hyperlode/luciebox/documentation/Drawings_F306/Luciebox_lid_layout_annotated_colour_font_autobahn.png

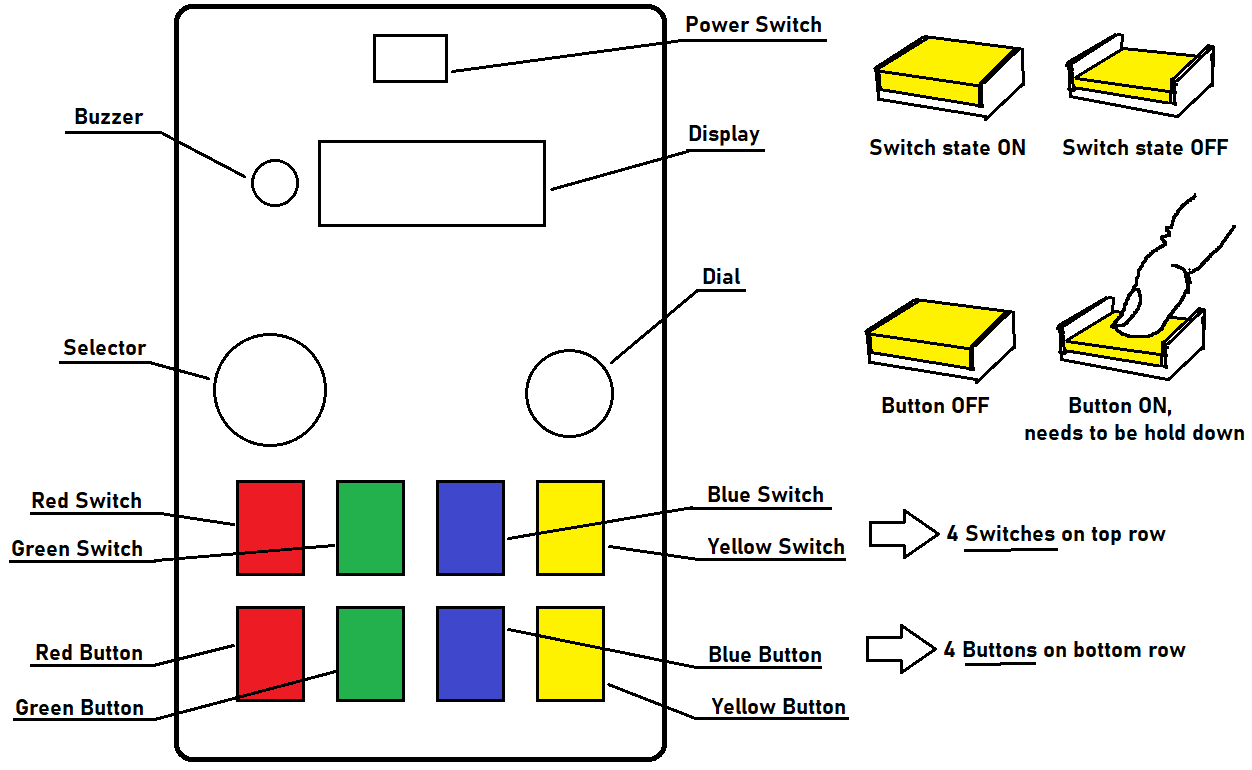
documentation/Drawings_F306/Luciebox_lid_layout_annotated_colour_font_autobahn.png
