hyperlode/luciebox/documentation/Drawings_F308/Luciebox_lid_layout_annotated_font_bahnschrift.png

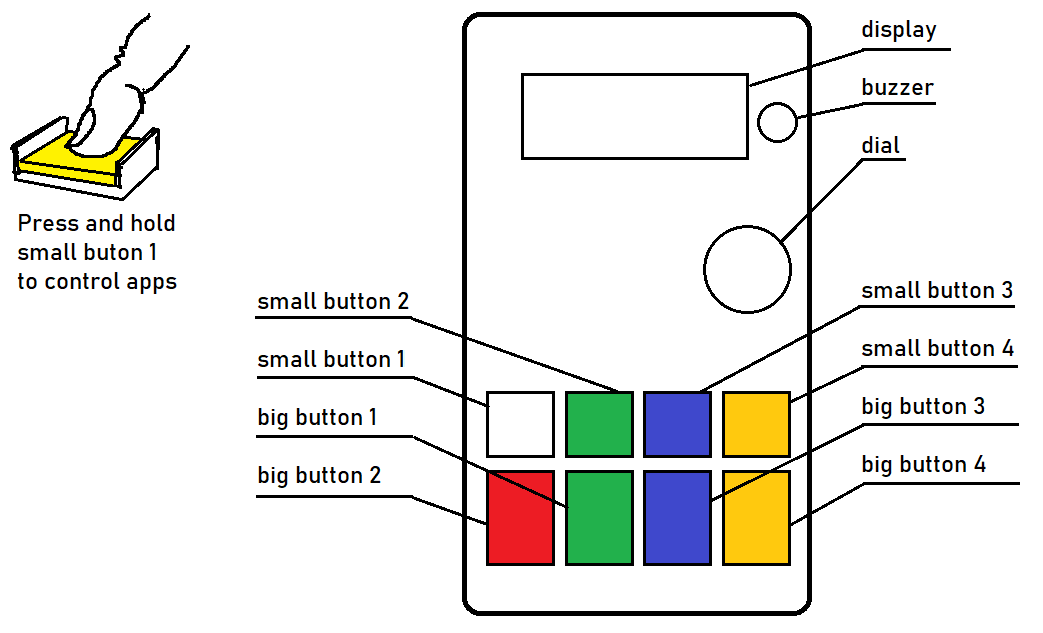
documentation/Drawings_F308/Luciebox_lid_layout_annotated_font_bahnschrift.png
