hyperlode/luciebox/pcb/v1 pcb with clouds - change pin 2 to A3 for segment B.jpg

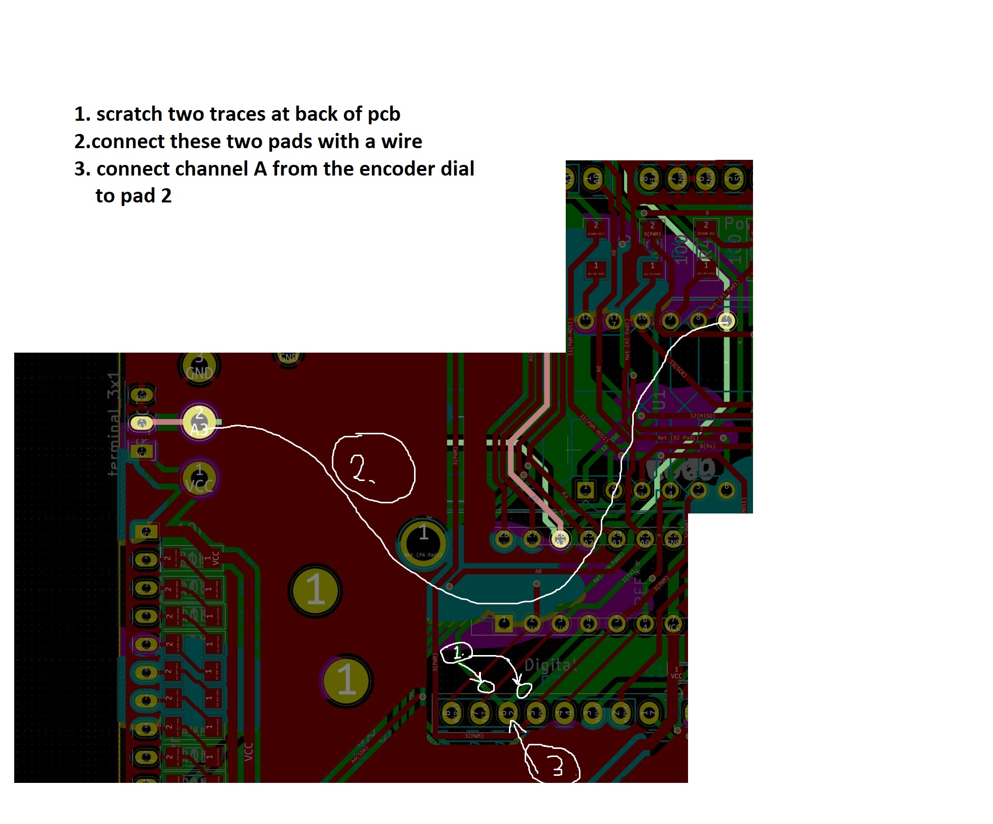
pcb/v1 pcb with clouds - change pin 2 to A3 for segment B.jpg
