hyperlode/luciebox/Luciebox/Apps.cpp

#include "Apps.h"
#include "PretbakSettings.h"

// ------------------------------------------------------------------------------------------------------------------------------------------------------
//		INIT AND ADMINISTRATION
// ------------------------------------------------------------------------------------------------------------------------------------------------------

Apps::Apps(){};

#ifdef ENABLE_SELECT_APPS_WITH_SELECTOR
void Apps::setPeripherals(BinaryInput binaryInputs[], RotaryEncoderDial *encoder_dial, DisplayManagement *ledDisp, LedMultiplexer5x8 *allLights, Buzzer *buzzer, PotentioSelector *selectorDial)
{
    this->buzzer = buzzer;
    this->binaryInputs = binaryInputs;
    this->encoder_dial = encoder_dial;
    this->ledDisp = ledDisp;
    this->allLights = allLights;
    this->selectorDial = selectorDial;

    textHandle = ledDisp->getDisplayTextBufHandle();
    decimalDotsHandle = ledDisp->getDecimalPointsHandle();
    inactivity_timer.setInitCountDownTimeSecs(indexToTimeSeconds(INACTIVITY_TIME_INDEX));
    resetInactivityTimer();
    always_on_timer.start();
}
#else
void Apps::setPeripherals(BinaryInput binaryInputs[], RotaryEncoderDial *encoder_dial, DisplayManagement *ledDisp, LedMultiplexer5x8 *allLights, Buzzer *buzzer)
{
    this->buzzer = buzzer;
    this->binaryInputs = binaryInputs;
    this->encoder_dial = encoder_dial;
    this->ledDisp = ledDisp;
    this->allLights = allLights;

    textHandle = ledDisp->getDisplayTextBufHandle();
    decimalDotsHandle = ledDisp->getDecimalPointsHandle();
    inactivity_timer.setInitCountDownTimeSecs(indexToTimeSeconds(INACTIVITY_TIME_INDEX));
    resetInactivityTimer();
    always_on_timer.start();

    appState = appStateInit;
}

#endif

#ifdef ENABLE_SELECT_APPS_WITH_SELECTOR
void Apps::appStateLoop()
{
    updateEveryAppCycleBefore();
    bool selector_changed = selectorDial->getValueChangedEdge();
    int selector_dial_value = selectorDial->getSelectorValue() - 1; // -1 because 13 resistor values for 12 pos knob, gnd is never switchted.

    bool shift_changed = (binaryInputsEdgeUp | binaryInputsEdgeDown) & (1 << BUTTON_INDEXED_SMALL_0); // l atching button acts as a "shift button" to have two apps per selector location

    // uint8_t selected_app = selector_dial_value * 2 + ((binaryInputsToggleValue & (1 << BUTTON_INDEXED_SMALL_0)) > 0);

    bool init_app_init = (selector_changed && (MODE_SETTINGS_SELECTOR != 10)) || (shift_changed && (selector_dial_value != 0)); // settings mode have no dual app available. So, don't init if shift button is toggled.  //&& (selector_dial_value != 11) and multitimer app

    this->app_init_edge = false;

    if (init_app_init)
    {
#ifdef ENABLE_SERIAL
        Serial.println("app select:");
        Serial.println(selected_app);
#endif

        buzzerSilentClearBuffer(); // The moment we switch apps, the sound goes off immediatly.

        // set to init state before a new app starts
        splash_screen_playing = true;
    }

    if (splash_screen_playing)
    {
        // do init routine (showing splash screen), if finished,end of init. Then continue to init of the chosen application
        splash_screen_playing = this->init_app(init_app_init, selector_dial_value);
        if (!splash_screen_playing)
        {
            this->initializeAppDataToDefault();
            this->app_init_edge = true;
            selected_app = selector_dial_value * 2 + ((binaryInputsToggleValue & (1 << BUTTON_INDEXED_SMALL_0)) > 0);
        }
    }

    // not as else statement, to have the init properly transferred after app beginning screen.
    if (!splash_screen_playing)
    {
        appSelector();
    }

    inactivityHandler();

    updateEveryAppCycleAfter();
}

#else

void Apps::appStateLoop()
{
    updateEveryAppCycleBefore();

#ifdef ENABLE_SELECT_APPS_WITH_SELECTOR
    bool selector_changed = selectorDial->getValueChangedEdge();
    int selector_dial_value = selectorDial->getSelectorValue() - 1; // -1 because 13 resistor values for 12 pos knob, gnd is never switchted.

#endif
    switch (appState)
    {

    case appStateInit:
    {
        this->selected_app = 1; // start with one, which also works for the non selector button setting

#ifdef ENABLE_EEPROM
#ifndef ENABLE_SELECT_APPS_WITH_SELECTOR
        // memorize active app
        this->selected_app = eeprom_read_byte(
            (uint8_t *)EEPROM_LUCIEBOX_ACTIVE_APP_AT_SHUTDOWN);
#endif
#endif
        appState = appSplashInit;
        selected_app_memory = 66;
        break;
    }

    case appSplashInit:
    {
#ifdef ENABLE_SERIAL
        Serial.println("app select:");
        Serial.println(selected_app);
#endif

        buzzerSilentClearBuffer(); // The moment we switch apps, the sound goes off immediatly.

        this->init_app(true, selected_app - 1); // selected app -1 because we start from 1
        // set to init state before a new app starts
        appState = appSplash;

        break;
    }

    case appSelection:
    {

        // reset app
        if ((binaryInputsEdgeUp & (1 << BUTTON_INDEXED_BIG_1)))
        {
            appState = appInit;
        }

        modifyValueUpDownWithButtonsBig2And3(&selected_app);
        selected_app += encoder_dial->getDelta();
        checkBoundaries(&selected_app, 1, 22, true);

        if (selected_app_edge != selected_app)
        {
            // set_blink_offset();
            blink_offset = millis();
        }
        selected_app_edge = selected_app;

        this->displayAllSegments = 0;

        if (switch_off)
        {
            setStandardTextToTextHANDLE(TEXT_OFF);
        }
        else
        {
            flashPictureToDisplayAllSegments(app_splash_screens + (selected_app - 1) * 4);
        }

        // activate switch off. shut down, will trigger when app selector is at negative edge
        if ((binaryInputsValue & (1 << BUTTON_INDEXED_BIG_0)))
        {
            switch_off = true;
        }

        if (!(binaryInputsValue & (1 << BUTTON_INDEXED_SMALL_0)))
        {
            // switch off. shut down
            if (switch_off)
            {
                shutdown();
            }

            if (selected_app == selected_app_memory)
            {
                // this->displayAllSegments = this->displayAllSegmentsBuffer;
                // displayAllSegmentsToScreen();
                appState = appRunning;
            }
            else
            {
                appState = appSplashInit;
            }
            selected_app_memory = selected_app;
        }

        // if (millis_quarter_second_period())
        // {
        //     lights |= 1 << LIGHT_BUTTON_BIG_0 | 1 << LIGHT_BUTTON_BIG_2 | 1 << LIGHT_BUTTON_BIG_3;
        // }
        button_light_blink_quarter_second_period(LIGHT_BUTTON_BIG_0);
        button_light_blink_quarter_second_period(LIGHT_BUTTON_BIG_2);
        button_light_blink_quarter_second_period(LIGHT_BUTTON_BIG_3);

        // if (millis_blink_250_750ms()){
        if ((millis() - blink_offset) > APP_NUMBER_TO_PICTOGRAM_DELAY_MILLIS)
        {
            ledDisp->setBinaryToDisplay(this->displayAllSegmentsBuffer);
            displayAllSegmentsToScreen();
        }
        else
        {
            ledDisp->setNumberToDisplayAsDecimal(selected_app);
        }

#ifndef ENABLE_SELECT_APPS_WITH_SELECTOR
        // small button lights off at app selection, whatever their toggle state is (but we do not want to lose the toggle state)
        for (uint8_t i = 5; i < 8; i++)
        {
            lights &= ~(1 << lights_indexed[i]);
        }
#endif

        break;
    }

    case appSplash:
    {

#ifdef ENABLE_SELECT_APPS_WITH_SELECTOR
        // do init routine (showing splash screen), if finished,end of init. Then continue to init of the chosen application
        splash_screen_playing = this->init_app(false, selector_dial_value);
        if (!splash_screen_playing)
        {
            // this->app_init_edge = true;
            appState = appInit;
            selected_app = selector_dial_value * 2 + ((binaryInputsToggleValue & (1 << BUTTON_INDEXED_SMALL_0)) > 0);
        }
#else
        // do init routine (showing splash screen), if finished,end of init. Then continue to init of the chosen application
        splash_screen_playing = this->init_app(false, selected_app - 1); // selected app -1 because we start from 1
        if (!splash_screen_playing)
        {
            appState = appInit;
        }

        if (binaryInputsValue & (1 << BUTTON_INDEXED_SMALL_0))
        {
            switch_off = false;
            appState = appSelection;
        }
#endif

        break;
    }

    case appInit:
    {
        this->initializeAppDataToDefault();
        this->app_init_edge = true;
        appState = appRunning;
        break;
    }

    case appRunning:
    {
        // not as else statement, to have the init properly transferred after app beginning screen.
        appSelector();
        this->app_init_edge = false; // global variable (saves memory) true at first run (set in another state )

#ifdef ENABLE_SELECT_APPS_WITH_SELECTOR

        bool shift_changed = (binaryInputsEdgeUp | binaryInputsEdgeDown) & (1 << BUTTON_INDEXED_SMALL_0); // l atching button acts as a "shift button" to have two apps per selector location

        // uint8_t selected_app = selector_dial_value * 2 + ((binaryInputsToggleValue & (1 << BUTTON_INDEXED_SMALL_0)) > 0);

        bool init_app_init = (selector_changed && (MODE_SETTINGS_SELECTOR != 10)) || (shift_changed && (selector_dial_value != 0)); // settings mode have no dual app available. So, don't init if shift button is toggled OR if we're visualizing the selector switch analog value in the settings app

        if (init_app_init)
        {
            appState = appSplashInit;
        }

#else
        if (binaryInputsValue & (1 << BUTTON_INDEXED_SMALL_0))
        {
            switch_off = false;
            appState = appSelection;
            // this->displayAllSegmentsBuffer = this->displayAllSegments; // if there is no change of app, the display state needs to be preserved
        }

#endif

        break;
    }
    }
    inactivityHandler();
    updateEveryAppCycleAfter();
}

#endif

void Apps::inactivityHandler()
{

    // for some timing aps, we want this watchdog timer to be disabled.
    // It's easily accomplished by resetting the inactivity timer in those apps continuously.

    // for every button press, the watchdog timer is reset
    if (binaryInputsEdgeUp)
    {
        resetInactivityTimer();
    }

    // watchdog timer elapsed
    if (inactivity_timer.getCountDownTimerElapsedAndRestart())
    {
        autoShutdown();
    }
}

void Apps::autoShutdown()
{
    // will shutdown if available and play an "I'm still on" sound if not.

#ifdef ENABLE_SOFT_POWER_OFF
    // auto power off

    uint8_t enable_auto_power_off = true;
#ifdef ENABLE_EEPROM
    enable_auto_power_off = !eeprom_read_byte((uint8_t *)EEPROM_LUCIEBOX_AUTO_POWER_OFF_DISABLED);
#endif
    if (enable_auto_power_off)
    {

        shutdown();
    }
    else
    {
        playSongHappyDryer();
    }

#else
    playSongHappyDryer();
#endif
}

void Apps::shutdown()
{
    // memorize active app to restart after shutdown
    eeprom_update_byte(
        (uint8_t *)EEPROM_LUCIEBOX_ACTIVE_APP_AT_SHUTDOWN,
        selected_app); // eeprom_update_... only writes if different from what's in address, no need to read to check.

    // add delay for eeprom to settle down? Fact is, without this delay, it does not save...
    for (uint16_t i = 0; i < 1000; i++)
    {
        resetInactivityTimer();
    }

    digitalWrite(PIN_POWER_ON_HOLD, LOW);
    digitalWrite(PIN_SELECTOR_BUTTON, LOW); // pull down input to enable transistor base to go low
    // normally, the device is switched off at this point. IF however, it's powered through an external device bypassing the auto power off mode, it should keep on working.

    for (uint16_t i = 0; i < 26000; i++)
    {
        resetInactivityTimer();
    }

    digitalWrite(PIN_POWER_ON_HOLD, HIGH);
    digitalWrite(PIN_SELECTOR_BUTTON, HIGH);
    // buzzerPlayDisappointment();
}

void Apps::appSelector()
{
    // #ifdef FUNCTION_POINTER_APP_SELECTION // problem: takes more memory than switch-case. AND init and initOnBigLatchInitToo not good. The solution would be to have all the apps without advanced init bundled together, and from certain selector value onwards and up, use "init"

    switch (selected_app)
    {
    case APP_SELECTOR_LETTERS_AND_CHARS:
#ifdef ENABLE_SCHOOL_APP
        this->modeCountingLettersAndChars();
#endif
        break;

    case APP_SELECTOR_SIMON:
#ifdef ENABLE_SIMON_APP
        this->modeSimon();
#endif
        break;

    case APP_SELECTOR_SOUND_NOTES:
        this->modeSoundNotes();
        break;

    case APP_SELECTOR_SOUND_COMPOSER:
        this->modeComposeSong();
        break;

    case APP_SELECTOR_STOPWATCH:
        stopwatch();
        break;

    case APP_SELECTOR_POMODORO:
#ifdef ENABLE_POMODORO
        pomodoroTimer();
#endif
        break;

    case APP_SELECTOR_RANDOMWORLD:
        this->modeRandomWorld();
        break;

    case APP_SELECTOR_TALLY_KEEPER:
#ifdef ENABLE_TALLY_KEEPER
        this->modeTallyKeeper();
#endif
        break;

    case APP_SELECTOR_GEIGER:
        this->modeGeiger();
        break;

    case APP_SELECTOR_HACK_TIME:
        this->modeHackTime();
        break;

    case APP_SELECTOR_SOUND_SONG:
        this->modeSoundSong();
        break;

    case APP_SELECTOR_DRAW:
        this->draw();
        break;

    case APP_SELECTOR_DRAW_GAME:
#ifdef ENABLE_DRAW_GAME
        this->drawGame();
#endif
        break;

    case APP_SELECTOR_MOVIE_MODE:
        this->modeMovie();
        break;

    case APP_SELECTOR_SETTING:
    case APP_SELECTOR_SETTING_TOO:
        this->modeSettings();
        break;

    case APP_SELECTOR_SOUND_METRONOME:
        this->modeMetronome();
        break;

    case APP_SELECTOR_SOUND_SEQUENCER:
        this->modeSequencer();
        break;

    case APP_SELECTOR_REACTION_GAME:
    case APP_SELECTOR_GUITAR_HERO:
#ifdef ENABLE_REACTION_APP
        this->modeReactionGame();
#endif
        break;

#ifdef ENABLE_TILT_APP
    case APP_SELECTOR_DREAMTIME:
        this->modeDreamtime();
        break;
    case APP_SELECTOR_TILT:
        this->tiltSwitchTest();
        break;
#else
    case APP_SELECTOR_DREAMTIME:
    case APP_SELECTOR_DREAMTIME_TOO:
        this->modeDreamtime();
        break;
#endif

#ifdef ENABLE_SHOOTOUT
    case APP_SELECTOR_SHOOTOUT:
        this->shootout();
        break;
#endif

    case APP_SELECTOR_MULTITIMER:
#ifdef ENABLE_MULTITIMER_STANDALONE_DEPRECATED
        this->miniMultiTimer();
#elif defined ENABLE_MULTITIMER_INTEGRATED
        this->multitimer_integrated();
#endif
        break;

    default:
        break;
    }
}

void Apps::resetInactivityTimer()
{
    inactivity_timer.start();
}

void Apps::updateEveryAppCycleBefore()
{
    binaryInputsEdgeUp = 0;
    binaryInputsEdgeDown = 0;
    binaryInputsValue = 0;
    binaryInputsToggleValue = 0;

    // it's important to realize the display is reset before every cycle. Do not forget to update it all the time.
    lights = 0x00;

    // load quick access bytes.
    for (uint8_t i = 0; i < 8; i++)
    {
        binaryInputsEdgeUp |= binaryInputs[buttons_indexed[i]].getEdgeUp() << i;
        binaryInputsEdgeDown |= binaryInputs[buttons_indexed[i]].getEdgeDown() << i;
        binaryInputsValue |= binaryInputs[buttons_indexed[i]].getValue() << i;
        binaryInputsToggleValue |= binaryInputs[buttons_indexed[i]].getToggleValue() << i;

#ifdef ENABLE_SELECT_APPS_WITH_SELECTOR
        lights |= binaryInputs[buttons_indexed[i]].getValue() << lights_indexed[i];

#else
        // by default: button lights on if activated
        if (i < 5)
        {
            // big buttons (i = 0,1,2,3) and control button (4) (small_0)
            // 5 instead of 4 because BUTTON_INDEXED_SMALL_0 is standard also only on if pressed.
            lights |= binaryInputs[buttons_indexed[i]].getValue() << lights_indexed[i];
        }
        else
        {
            // small buttons (i=5,6,7)
            lights |= binaryInputs[buttons_indexed[i]].getToggleValue() << lights_indexed[i];
        }
#endif
    }

    // big_buttons_mask =
    // byte big_buttons_mask = 1 << BUTTON_INDEXED_BIG_0 | 1 << BUTTON_INDEXED_BIG_1 | 1 << BUTTON_INDEXED_BIG_2 | 1 << BUTTON_INDEXED_BIG_3;

    binaryInputsEdgeUpBigButtonIndex = -1;
    // get index of pressed button.
    for (int i = 0; i < BIG_BUTTONS_COUNT; i++)
    {
        // WARNING: If button presses are pressed in too quick succession (and processed in the same cycle), only one edge is captured.
        // ONLY USE IN SLOW APPS
        if (binaryInputsEdgeUp & 1 << i)
        {
            // #ifdef ENABLE_SERIAL
            //             Serial.println(i);
            // #endif
            binaryInputsEdgeUpBigButtonIndex = i;
        }
    }

    setBlankDisplay();
}

void Apps::updateEveryAppCycleAfter()
{
    // setLedArray();
    ledDisp->setLedArray(lights);
}

void Apps::initializeAppDataToDefault()
{
    // allLights->setBrightness(0, false); // disable because it annoys me:)

    initiateCountDowntimerWith500Millis(&general_timer_1); //

    // buzzer  (buzzer off at init of splash screen)
    buzzer->setSpeedRatio(2);
    buzzer->setTranspose(0);

    // encoder
    encoder_dial->setRange(1023, true); // allow overflow. (this makes it different from the limited potentio.)
    encoder_dial->setValue(0);

    fill8BytesArrayWithZero();

    randomSeed(millis());

    encoder_dial->setSensitivity(8);

    // all shared variables to zero or false

    general_boolean1 = 0;
    general_boolean2 = 0;
    general_boolean3 = 0;
    general_boolean4 = 0;
    general_int16_t_1 = 0;
    general_int16_t_2 = 0;
    general_int16_t_3 = 0;
    general_int16_t_4 = 0;
    general_uint16_t_1 = 0;
    general_uint16_t_2 = 0;
    general_uint8_t_1 = 0;
    general_uint8_t_2 = 0;
    general_uint8_t_3 = 0;
    general_uint8_t_4 = 0;
    general_uint8_t_5 = 0;
    general_int8_t_1 = 0;
    general_long_1 = 0;
    general_long_2 = 0;

    // simulated l atching buttons reset. This is the great advantage of not having l atching buttons. The app starts in a truly blank state when initialized.
    for (uint8_t i = 0; i < 8; i++)
    {
        binaryInputs[buttons_indexed[i]].setToggleValue(0);
    }
}

bool Apps::init_app(bool init, uint8_t selector)
{
    // shows animated introduction splash screen at each main app startup
    // returns true as long as it is busy

    if (init)
    {
        // init of the init_app..
        this->displayAllSegments = 0;
        flashPictureToDisplayAllSegments(app_splash_screens + selector * 4);

        // initialize list
        randomSequence(FADE_IN_RANDOM_LIST, 32);

        // INIT_SPLASH_ANIMATION_STEP = 0;
        // INIT_SPLASH_LIGHTS_STEP = 0;

        this->TIMER_INIT_APP.start(-20);
    }

    // advance one frame
    if (this->TIMER_INIT_APP.getCountDownTimerElapsedAndRestart())
    {
        INIT_SPLASH_LIGHTS_STEP++;
        INIT_SPLASH_ANIMATION_STEP++;
    }

#ifdef ENABLE_SELECT_APPS_WITH_SELECTOR
    if (INIT_SPLASH_ANIMATION_STEP < 5)
    {
        lights = 0xff;
        // all lights on
        ledDisp->setBinaryToDisplay(0xFFFFFFFF); // use fade in as fade out to set text.
    }
    else
#endif
        if (INIT_SPLASH_ANIMATION_STEP < 23)
    {
        // show app splash screen
        ledDisp->setBinaryToDisplay(this->displayAllSegments);

        // ledDisp->setNumberToDisplayAsDecimal(MODE_SETTINGS_SELECTOR);
        // textBufToDisplay();

        lights = 0xff;
    }
    else if (INIT_SPLASH_ANIMATION_STEP < 55)
    {
        // fade out
        ledDisp->setBinaryToDisplay(~this->fadeInList(INIT_SPLASH_ANIMATION_STEP - 24, ~this->displayAllSegments, this->FADE_IN_RANDOM_LIST));
        INIT_APP_LIGHTS_COUNTER = ((32 - (INIT_SPLASH_ANIMATION_STEP - 22)) / 4);
        for (uint8_t i = 0; i <= INIT_APP_LIGHTS_COUNTER; i++)
        {
            lights |= 0x1 << lights_indexed_as_installed[i];
        }
    }
    else
    {
        return false;
    }

#ifdef ENABLE_SELECT_APPS_WITH_SELECTOR
    // hold down big button to freeze app splash screen (easier to rotate knob to search for desired app)
    byte big_buttons_mask = 1 << BUTTON_INDEXED_BIG_0 | 1 << BUTTON_INDEXED_BIG_1 | 1 << BUTTON_INDEXED_BIG_2 | 1 << BUTTON_INDEXED_BIG_3;
    if ((binaryInputsValue & big_buttons_mask) > 0)
    {
        INIT_SPLASH_ANIMATION_STEP = 6;
        lights = 0x00;
        lights |= 0x1 << lights_indexed_as_installed[(INIT_SPLASH_LIGHTS_STEP % 32) / 4];
        // lights	|= 0x1 << lights_indexed_as_installed[((INIT_SPLASH_LIGHTS_STEP+16) %32)/4];
    }
#endif

    return true;
}

// ------------------------------------------------------------------------------------------------------------------------------------------------------
//		ACTUAL APPS
// ------------------------------------------------------------------------------------------------------------------------------------------------------

void Apps::modeDreamtime()
{
    // baby activity for those who can not yet rotate the selector dial. (the shift button makes it stay in the same app).

    if (this->app_init_edge)
    {
        MODE_DREAMTIME_FADE_IN_ELSE_FADE_OUT = true;
        MODE_DREAMTIME_STEP = random(3, 31); // let's not start with an empty screen
    }

    modifyValueUpDownWithButtonsBig2And3(&MODE_DREAMTIME_STEP);

    if (!(binaryInputsToggleValue & (1 << BUTTON_INDEXED_SMALL_3)))
    {
        if (this->TIMER_DREAMTIME.getCountDownTimerElapsedAndRestart())
        {
            MODE_DREAMTIME_STEP++;
        }

        dialOnEdgeChangeInitTimerPercentage(&TIMER_DREAMTIME);
    }
    else
    {
        MODE_DREAMTIME_STEP += encoder_dial->getDelta();
    }

    if (!checkBoundaries(&MODE_DREAMTIME_STEP, 0, 31, true))
    {
        MODE_DREAMTIME_FADE_IN_ELSE_FADE_OUT = !MODE_DREAMTIME_FADE_IN_ELSE_FADE_OUT;
        randomSequence(MODE_DREAMTIME_RANDOM_LIST, 32);
    }

    if (binaryInputsEdgeUp & (1 << BUTTON_INDEXED_SMALL_1))
    {
        if (binaryInputsToggleValue & (1 << BUTTON_INDEXED_SMALL_1))
        {
            loadBuzzerTrack(SONG_ALPHABET);
        }
        else
        {
            playSongHappyDryer();
        }
    }

    if (!(binaryInputsToggleValue & (1 << BUTTON_INDEXED_SMALL_2)))
    {
        if (MODE_DREAMTIME_STEP_MEMORY != MODE_DREAMTIME_STEP)
        {
            // PROBLEM: random notes buffer and song buffer are the same bytes list! -->hence the weird behaviour
            buzzerSilentClearBufferAndAddNote(MODE_DREAMTIME_RANDOM_LIST[MODE_DREAMTIME_STEP]); // 60
            // if(buzzer->buzzerBufferDonePlaying()){
            //     addNoteToBuzzer(MODE_DREAMTIME_RANDOM_LIST[MODE_DREAMTIME_STEP]); //60

            // }
        }
    }

    uint32_t display_binary = fadeInList(MODE_DREAMTIME_STEP, 0, MODE_DREAMTIME_RANDOM_LIST);

    MODE_DREAMTIME_STEP_MEMORY = MODE_DREAMTIME_STEP;

    if (!MODE_DREAMTIME_FADE_IN_ELSE_FADE_OUT)
    {
        display_binary = ~display_binary;
    }

    if (binaryInputsValue & (1 << BUTTON_INDEXED_BIG_1))
    {
        display_binary = 0xFFFFFFFF;
        buzzerPlayApproval();
    }

    if (binaryInputsValue & (1 << BUTTON_INDEXED_BIG_0))
    {
        display_binary = 0x795E3F38; // self glorification time.
    }

    ledDisp->setBinaryToDisplay(display_binary);
}

#ifdef ENABLE_POMODORO

#ifndef ENABLE_SELECT_APPS_WITH_SELECTOR
void Apps::pomodoroTimer()
{
    uint8_t display_mode = POMODORO_DISPLAY_TIMER;

#ifdef POMODORO_ENABLE_HOURGLASS
    this->displayAllSegments = 0;
#endif

    lights = 0;

    if (encoder_dial->getDelta() != 0)
    {
        set_blink_offset();
    }

    if (this->app_init_edge)
    {
#ifdef ENABLE_EEPROM
        POMODORO_MAIN_CLOCK_TIME_INDEX = eeprom_read_byte((uint8_t *)EEPROM_POMODORO_INIT_TIME_INDEX);
        POMODORO_PAUSE_TIME_INDEX = eeprom_read_byte((uint8_t *)EEPROM_POMODORO_PAUSE_TIME_INDEX);
        POMODORO_PROBABILITY_BEEP_INTERVAL_INDEX = eeprom_read_byte((uint8_t *)EEPROM_POMODORO_RND_BEEP_TIME_INDEX);
#else
        POMODORO_MAIN_CLOCK_TIME_INDEX = POMODORO_INIT_DEFAULT_TIME_INDEX;
        POMODORO_PAUSE_TIME_INDEX = POMODORO_PAUSE_DEFAULT_TIME_INDEX;
        POMODORO_PROBABILITY_BEEP_INTERVAL_INDEX = POMODORO_PROBABILITY_BEEP_INTERVAL_DEFAULT_TIME_INDEX;
#endif
    }

    // acts as ticking mute on / off
    if (binaryInputsToggleValue & (1 << BUTTON_INDEXED_BIG_1))
    {
        lights |= 1 << LIGHT_BUTTON_BIG_1;
    }

    POMODORO_TIMER_TICKING = binaryInputsToggleValue & (1 << BUTTON_INDEXED_SMALL_3);
    // in main menu or timing? (run main menu at least once at init. Even when start button started) to initialize variables depending on settings buttons

    if (POMODORO_TIMER_TICKING && !app_init_edge)
    {
        // never auto power off when timer is on
        resetInactivityTimer();

        // pomodoro timer running

        if (!POMODORO_FIRST_TICKING_CYCLING_DONE)
        {
            POMODORO_FIRST_TICKING_CYCLING_DONE = true;
            POMODORO_IN_BREAK = false;
            // just started timing
            POMODORO_TIMER.start();
#ifdef ENABLE_EEPROM
            eeprom_update_byte((uint8_t *)EEPROM_POMODORO_INIT_TIME_INDEX, POMODORO_MAIN_CLOCK_TIME_INDEX);
            eeprom_update_byte((uint8_t *)EEPROM_POMODORO_PAUSE_TIME_INDEX, POMODORO_PAUSE_TIME_INDEX);
            eeprom_update_byte((uint8_t *)EEPROM_POMODORO_RND_BEEP_TIME_INDEX, POMODORO_PROBABILITY_BEEP_INTERVAL_INDEX);
#endif
        }

        if (binaryInputsEdgeUp & (1 << BUTTON_INDEXED_BIG_2))
        {
            POMODORO_STATS_WORKING_BAD++;
        }
        if (binaryInputsEdgeUp & (1 << BUTTON_INDEXED_BIG_3))
        {
            POMODORO_STATS_WORKING_GOOD++;
        }

        if ((binaryInputsValue & (1 << BUTTON_INDEXED_BIG_2)))
        {
            display_mode = POMODORO_DISPLAY_SHOW_BAD;
        }
        if ((binaryInputsValue & (1 << BUTTON_INDEXED_BIG_3)))
        {
            display_mode = POMODORO_DISPLAY_SHOW_GOOD;
        }

        // ticking sound / random checkup-beep
        // uint8_t tick_duration = encoder_dial->getValueLimited(160, false) / 2; // was 40, but set to 80 for less sensitivity. do again divide by four to limit options.
        // tick_duration += encoder
        stepChange(&POMODORO_SOUND, encoder_dial->getDelta(), 0, 80, false);
        bool tick_twice_a_second = POMODORO_SOUND > 40;
        // tick_duration = tick_duration % 40;

        if (POMODORO_TIMER.getEdgeSinceLastCallFirstGivenHundredsPartOfSecond(500, true, tick_twice_a_second))
        {
#ifdef POMODORO_ENABLE_HOURGLASS
            POMODORO_VISUAL_TIMER_PROGRESS =
                (uint8_t)((
                    (17 * POMODORO_TIMER.getTimeMillis()) / POMODORO_TIMER.getInitTimeMillis())

                );
#endif

            if (POMODORO_PROBABILITY_BEEP_INTERVAL_INDEX > 0)
            {
                if (random(0, indexToTimeSeconds(POMODORO_PROBABILITY_BEEP_INTERVAL_INDEX) * 2) <= 1 - (tick_twice_a_second))
                {
                    // random has 0 included. as we have to take into account the double ticking,
                    // calculate the probability in half a seconds. i.e.  one every minute: (0,120)
                    buzzerPlayDisappointment();
                };
            }

            // no sound when zero
            if (buzzer->buzzerBufferDonePlaying() &&                     // if end of clock signal sounds, no ticking! erase to optimize memory
                !(binaryInputsToggleValue & (1 << BUTTON_INDEXED_BIG_1)) // mute on / off
            )
            {
                // buzzer->playTone(500, 1 + (unsigned long)POMODORO_SOUND % 40); // works well
                buzzerPlayTone(500, 1 + (unsigned long)POMODORO_SOUND % 40);
            }
        }

        // timer
        if (getCountDownTimerHasElapsed(&POMODORO_TIMER))
        {
            POMODORO_IN_BREAK = !POMODORO_IN_BREAK;
            if (POMODORO_IN_BREAK)
            {
                // finished main pomodoro

                playSongHappyDryer();
                if (POMODORO_PAUSE_TIME_INDEX > 0)
                {
                    POMODORO_TIMER.setInitCountDownTimeSecs(indexToTimeSeconds(POMODORO_PAUSE_TIME_INDEX));
                    POMODORO_TIMER.start();
                }
                else
                {

#ifndef ENABLE_SELECT_APPS_WITH_SELECTOR
                    // with l atching buttons, we need to unlatch the button physically. But, with m omentary buttons, we can unlatch the button with software
                    binaryInputs[BUTTON_SMALL_3].setToggleValue(0);

#endif
                    POMODORO_TIMER.reset();
                    POMODORO_IN_BREAK = false;
                }
            }
            else
            {
                // coming out of break. Not executed at starting Pomodoro by switch.

                loadBuzzerTrack(SONG_ATTACK);
                POMODORO_TIMER.setInitCountDownTimeSecs(indexToTimeSeconds(POMODORO_MAIN_CLOCK_TIME_INDEX));
                POMODORO_TIMER.start();
            }
        }

        // inviting lights to press the buttons
        lights |= 1 << LIGHT_BUTTON_BIG_2;
        lights |= 1 << LIGHT_BUTTON_BIG_3;
#ifdef POMODORO_ENABLE_HOURGLASS
        if (binaryInputsToggleValue & (1 << BUTTON_INDEXED_BIG_0))
        {
            display_mode = POMODORO_DISPLAY_TIMER_HOURGLASS;
        }

#endif
    }
    else
    {
        // in main menu
        POMODORO_FIRST_TICKING_CYCLING_DONE = false;
        POMODORO_TIMER.reset();
        POMODORO_TIMER.setInitCountDownTimeSecs(indexToTimeSeconds(POMODORO_MAIN_CLOCK_TIME_INDEX));

        // set timer up for change
        int16_t *active_seconds_modifier = &POMODORO_MAIN_CLOCK_TIME_INDEX; // normal time setting is default option
        if ((binaryInputsValue & (1 << BUTTON_INDEXED_SMALL_2)))
        {

            active_seconds_modifier = &POMODORO_PAUSE_TIME_INDEX;
            display_mode = POMODORO_DISPLAY_PAUSE_INIT_SECS;
        }
        else if ((binaryInputsValue & (1 << BUTTON_INDEXED_SMALL_1)))
        {

            active_seconds_modifier = &POMODORO_PROBABILITY_BEEP_INTERVAL_INDEX;
            display_mode = POMODORO_DISPLAY_BEEP_PROBABILITY;
        }

        // look for value change with encoder dial
        encoderDialRefreshTimeIndex(active_seconds_modifier);

        // show performance results
        if ((binaryInputsValue & (1 << BUTTON_INDEXED_BIG_2)))
        {
            display_mode = POMODORO_DISPLAY_SHOW_BAD;
        }
        if ((binaryInputsValue & (1 << BUTTON_INDEXED_BIG_3)))
        {
            display_mode = POMODORO_DISPLAY_SHOW_GOOD;
        }

        // blinking small button invites user to start
        // if (millis_half_second_period())
        // {
        //     lights |= 1 << LIGHT_BUTTON_SMALL_3;
        // }
        button_light_blink_half_second_period(LIGHT_BUTTON_SMALL_3);
    }

    // display
    switch (display_mode)
    {
    case POMODORO_DISPLAY_TIMER_HOURGLASS:
    {
        setStandardTextToTextBuf(TEXT_SPACES);
#ifdef POMODORO_ENABLE_HOURGLASS
        // always set to buffer. later on it's decided if it's displayed or not.
        // for (uint8_t i=0;i<POMODORO_VISUAL_TIMER_PROGRESS;i++)
        // {
        // 	this->displayAllSegments |= 1UL << i;
        // }
        // this->displayAllSegments &= ~(1UL << 15); // keep seconds blinker spot clear
        // setBlankDisplay();
        lights |= 1 << LIGHT_BUTTON_BIG_0;
        flashPictureToDisplayAllSegments(disp_4digits_animations + FADE_IN_OFFSET + (POMODORO_VISUAL_TIMER_PROGRESS) * 4);
#endif
    }
    break;

    case POMODORO_DISPLAY_TIMER:
    {
        POMODORO_TIMER.getTimeString(textHandle);
        if (POMODORO_IN_BREAK)
        {
            setStandardTextToTextBuf(TEXT_PAUS);
        }
        else
        {
            POMODORO_TIMER.getTimeString(textBuf);
        }
    }
    break;

    case POMODORO_DISPLAY_PAUSE_INIT_SECS:
    {
        timeSecondsToClockString(textHandle, indexToTimeSeconds(POMODORO_PAUSE_TIME_INDEX));
        setStandardTextToTextBuf(TEXT_PAUS);
    }
    break;

    case POMODORO_DISPLAY_BEEP_PROBABILITY:
    {
        timeSecondsToClockString(textHandle, indexToTimeSeconds(POMODORO_PROBABILITY_BEEP_INTERVAL_INDEX));
        setStandardTextToTextBuf(TEXT_RANDOM_BEEP);
    }
    break;

    case POMODORO_DISPLAY_SHOW_GOOD:
    {
        setStandardTextToTextBuf(TEXT_YES);
        ledDisp->numberToBufAsDecimal(textHandle, POMODORO_STATS_WORKING_GOOD);
    }
    break;

    case POMODORO_DISPLAY_SHOW_BAD:
    {
        setStandardTextToTextBuf(TEXT_NO);
        ledDisp->numberToBufAsDecimal(textHandle, POMODORO_STATS_WORKING_BAD);
    }
    break;

    default:
        break;
    }

    displayTimerSecondsBlinker(&POMODORO_TIMER);

    // leds
    if (POMODORO_PROBABILITY_BEEP_INTERVAL_INDEX > 0)
    {
        lights |= 1 << LIGHT_BUTTON_SMALL_1;
    }
    if (POMODORO_PAUSE_TIME_INDEX > 0)
    {
        lights |= 1 << LIGHT_BUTTON_SMALL_2;
    }

#ifdef POMODORO_ENABLE_HOURGLASS
    displayAllSegmentsToScreen();
    if (millis_blink_250_750ms())
    {
        textBufToDisplay();
    }

#else
    if (millis_blink_250_750ms())
    {
        textBufToDisplay();
    }
#endif
}

#else // ENABLE_SELECT_APPS_WITH_SELECTOR
void Apps::pomodoroTimer()
{
    uint8_t display_mode = POMODORO_DISPLAY_TIMER;

#ifdef POMODORO_ENABLE_HOURGLASS
    this->displayAllSegments = 0;
#endif

    if (encoder_dial->getDelta() != 0)
    {
        set_blink_offset();
    }

    if (this->app_init_edge)
    {
#ifdef ENABLE_EEPROM
        POMODORO_MAIN_CLOCK_TIME_INDEX = eeprom_read_byte((uint8_t *)EEPROM_POMODORO_INIT_TIME_INDEX);
        POMODORO_PAUSE_TIME_INDEX = eeprom_read_byte((uint8_t *)EEPROM_POMODORO_PAUSE_TIME_INDEX);
        POMODORO_PROBABILITY_BEEP_INTERVAL_INDEX = eeprom_read_byte((uint8_t *)EEPROM_POMODORO_RND_BEEP_TIME_INDEX);
#else
        POMODORO_MAIN_CLOCK_TIME_INDEX = POMODORO_INIT_DEFAULT_TIME_INDEX;
        POMODORO_PAUSE_TIME_INDEX = POMODORO_PAUSE_DEFAULT_TIME_INDEX;
        POMODORO_PROBABILITY_BEEP_INTERVAL_INDEX = POMODORO_PROBABILITY_BEEP_INTERVAL_DEFAULT_TIME_INDEX;
#endif
    }

    POMODORO_AUTO_RESTART_ENABLED = binaryInputsToggleValue & (1 << BUTTON_INDEXED_SMALL_1);
    // #ifdef ENABLE_SELECT_APPS_WITH_SELECTOR
    POMODORO_TIMER_TICKING = binaryInputsToggleValue & (1 << BUTTON_INDEXED_SMALL_3);

    // #endif
    //  in main menu or timing? (run main menu at least once at init. Even when start button started) to initialize variables depending on settings buttons

    if (POMODORO_TIMER_TICKING && !app_init_edge)
    {
        // never auto power off when timer is on
        resetInactivityTimer();

        // pomodoro timer running

        if (!POMODORO_FIRST_TICKING_CYCLING_DONE)
        {
            POMODORO_FIRST_TICKING_CYCLING_DONE = true;
            POMODORO_IN_BREAK = false;
            // just started timing
            POMODORO_TIMER.start();
#ifdef ENABLE_EEPROM
            eeprom_update_byte((uint8_t *)EEPROM_POMODORO_INIT_TIME_INDEX, POMODORO_MAIN_CLOCK_TIME_INDEX);
            eeprom_update_byte((uint8_t *)EEPROM_POMODORO_PAUSE_TIME_INDEX, POMODORO_PAUSE_TIME_INDEX);
            eeprom_update_byte((uint8_t *)EEPROM_POMODORO_RND_BEEP_TIME_INDEX, POMODORO_PROBABILITY_BEEP_INTERVAL_INDEX);
#endif
        }

        if (binaryInputsEdgeUp & (1 << BUTTON_INDEXED_BIG_2))
        {
            POMODORO_STATS_WORKING_BAD++;
        }
        if (binaryInputsEdgeUp & (1 << BUTTON_INDEXED_BIG_3))
        {
            POMODORO_STATS_WORKING_GOOD++;
        }

        if ((binaryInputsValue & (1 << BUTTON_INDEXED_BIG_0)) ||
            (binaryInputsValue & (1 << BUTTON_INDEXED_BIG_2)))
        {
            display_mode = POMODORO_DISPLAY_SHOW_BAD;
        }

        if ((binaryInputsValue & (1 << BUTTON_INDEXED_BIG_1)) ||
            (binaryInputsValue & (1 << BUTTON_INDEXED_BIG_3)))
        {
            display_mode = POMODORO_DISPLAY_SHOW_GOOD;
        }

        // ticking sound / random checkup-beep
        // uint8_t tick_duration = encoder_dial->getValueLimited(160, false) / 2; // was 40, but set to 80 for less sensitivity. do again divide by four to limit options.
        // tick_duration += encoder
        stepChange(&POMODORO_SOUND, encoder_dial->getDelta(), 0, 80, false);
        bool tick_twice_a_second = POMODORO_SOUND > 40;
        // tick_duration = tick_duration % 40;

        if (POMODORO_TIMER.getEdgeSinceLastCallFirstGivenHundredsPartOfSecond(500, true, tick_twice_a_second))
        {
#ifdef POMODORO_ENABLE_HOURGLASS
            POMODORO_VISUAL_TIMER_PROGRESS =
                (uint8_t)((
                    (17 * POMODORO_TIMER.getTimeMillis()) / POMODORO_TIMER.getInitTimeMillis())

                );
#ifdef ENABLE_SERIAL
            Serial.println(POMODORO_VISUAL_TIMER_PROGRESS);
            Serial.println(this->displayAllSegments, BIN);
#endif
#endif

            if (POMODORO_PROBABILITY_BEEP_INTERVAL_INDEX > 0)
            {
                if (random(0, indexToTimeSeconds(POMODORO_PROBABILITY_BEEP_INTERVAL_INDEX) * 2) <= 1 - (tick_twice_a_second))
                {
                    // random has 0 included. as we have to take into account the double ticking,
                    // calculate the probability in half a seconds. i.e.  one every minute: (0,120)
                    buzzerPlayDisappointment();
                };
            }

            // no sound when zero
            if (buzzer->buzzerBufferDonePlaying()) // if end of clock signal sounds, no ticking! erase to optimize memory
            {
                buzzer->playTone(500, 1 + (unsigned long)POMODORO_SOUND % 40); // works well
            }
        }

        // timer
        if (getCountDownTimerHasElapsed(&POMODORO_TIMER))
        {
            POMODORO_IN_BREAK = !POMODORO_IN_BREAK;
            if (POMODORO_IN_BREAK)
            {
                // finished main pomodoro

                playSongHappyDryer();
                if (POMODORO_AUTO_RESTART_ENABLED)
                {
                    POMODORO_TIMER.setInitCountDownTimeSecs(indexToTimeSeconds(POMODORO_PAUSE_TIME_INDEX));
                    POMODORO_TIMER.start();
                }
                else
                {

#ifndef ENABLE_SELECT_APPS_WITH_SELECTOR
                    // with l atching buttons, we need to unlatch the button physically. But, with big buttons, we can unlatch the button with software
                    binaryInputs[BUTTON_SMALL_3].setToggleValue(0);

#endif
                    POMODORO_TIMER.reset();
                    POMODORO_IN_BREAK = false;
                }
            }
            else
            {
                // coming out of break. Not executed at starting Pomodoro by switch.

                loadBuzzerTrack(SONG_ATTACK);
                POMODORO_TIMER.setInitCountDownTimeSecs(indexToTimeSeconds(POMODORO_MAIN_CLOCK_TIME_INDEX));
                POMODORO_TIMER.start();
            }
        }

        // inviting lights to press the buttons
        lights |= 1 << LIGHT_BUTTON_BIG_2;
        lights |= 1 << LIGHT_BUTTON_BIG_3;
    }
    else
    {
        // in main menu
        POMODORO_FIRST_TICKING_CYCLING_DONE = false;
        POMODORO_TIMER.reset();
        POMODORO_TIMER.setInitCountDownTimeSecs(indexToTimeSeconds(POMODORO_MAIN_CLOCK_TIME_INDEX));

        // set timer up for change
        int16_t *active_seconds_modifier = &POMODORO_MAIN_CLOCK_TIME_INDEX; // normal time setting is default option
        if ((binaryInputsValue & (1 << BUTTON_INDEXED_BIG_0)))
        {
            active_seconds_modifier = &POMODORO_PAUSE_TIME_INDEX;
            display_mode = POMODORO_DISPLAY_PAUSE_INIT_SECS;
        }
        else if ((binaryInputsValue & (1 << BUTTON_INDEXED_BIG_1)))
        {
            active_seconds_modifier = &POMODORO_PROBABILITY_BEEP_INTERVAL_INDEX;
            display_mode = POMODORO_DISPLAY_BEEP_PROBABILITY;
        }

        // look for value change with encoder dial
        encoderDialRefreshTimeIndex(active_seconds_modifier);

        // show performance results
        if ((binaryInputsValue & (1 << BUTTON_INDEXED_BIG_2)))
        {
            display_mode = POMODORO_DISPLAY_SHOW_BAD;
        }
        if ((binaryInputsValue & (1 << BUTTON_INDEXED_BIG_3)))
        {
            display_mode = POMODORO_DISPLAY_SHOW_GOOD;
        }

        // blinking small button invites user to start
        if (millis_half_second_period())
        {
            lights |= 1 << LIGHT_BUTTON_SMALL_3;
        }
    }
#ifdef POMODORO_ENABLE_HOURGLASS
    if (binaryInputsToggleValue & (1 << BUTTON_INDEXED_SMALL_2))
    {
        display_mode = POMODORO_DISPLAY_TIMER_HOURGLASS;
    }
#endif

    // display
    switch (display_mode)
    {
    case POMODORO_DISPLAY_TIMER_HOURGLASS:
    {
        setStandardTextToTextBuf(TEXT_SPACES);
#ifdef POMODORO_ENABLE_HOURGLASS
        // always set to buffer. later on it's decided if it's displayed or not.
        // for (uint8_t i=0;i<POMODORO_VISUAL_TIMER_PROGRESS;i++)
        // {
        // 	this->displayAllSegments |= 1UL << i;
        // }
        // this->displayAllSegments &= ~(1UL << 15); // keep seconds blinker spot clear
        // setBlankDisplay();
        flashPictureToDisplayAllSegments(disp_4digits_animations + FADE_IN_OFFSET + (POMODORO_VISUAL_TIMER_PROGRESS) * 4);
#endif
    }
    break;

    case POMODORO_DISPLAY_TIMER:
    {
        POMODORO_TIMER.getTimeString(textHandle);
        if (POMODORO_IN_BREAK)
        {
            setStandardTextToTextBuf(TEXT_PAUS);
        }
        else
        {
            POMODORO_TIMER.getTimeString(textBuf);
        }
    }
    break;

    case POMODORO_DISPLAY_PAUSE_INIT_SECS:
    {
        timeSecondsToClockString(textHandle, indexToTimeSeconds(POMODORO_PAUSE_TIME_INDEX));
        setStandardTextToTextBuf(TEXT_PAUS);
    }
    break;

    case POMODORO_DISPLAY_BEEP_PROBABILITY:
    {
        timeSecondsToClockString(textHandle, indexToTimeSeconds(POMODORO_PROBABILITY_BEEP_INTERVAL_INDEX));
        setStandardTextToTextBuf(TEXT_RANDOM_BEEP);
    }
    break;

    case POMODORO_DISPLAY_SHOW_GOOD:
    {
        setStandardTextToTextBuf(TEXT_YES);
        ledDisp->numberToBufAsDecimal(textHandle, POMODORO_STATS_WORKING_GOOD);
    }
    break;

    case POMODORO_DISPLAY_SHOW_BAD:
    {
        setStandardTextToTextBuf(TEXT_NO);
        ledDisp->numberToBufAsDecimal(textHandle, POMODORO_STATS_WORKING_BAD);
    }
    break;

    default:
        break;
    }

    displayTimerSecondsBlinker(&POMODORO_TIMER);

    // leds
    if (POMODORO_PROBABILITY_BEEP_INTERVAL_INDEX > 0)
    {
        lights |= 1 << LIGHT_BUTTON_BIG_1;
    }

#ifdef POMODORO_ENABLE_HOURGLASS
    // if (POMODORO_ENABLE_HOURGLASS_VISUALS){
    displayAllSegmentsToScreen();

    // }else{
    if (millis_blink_250_750ms())
    {
        textBufToDisplay();
    }
    // }

#else
    if (millis_blink_250_750ms())
    {
        textBufToDisplay();
    }
#endif
}
#endif // #ifndef ENABLE_SELECT_APPS_WITH_SELECTOR
#endif // enable pomodoro

void Apps::encoderDialRefreshTimeIndex(int16_t *indexHolder)
{
    // actually change the set up timer

    stepChange(indexHolder, encoder_dial->getDelta(), 0, TIME_INDECES_COUNT, false);
}

void Apps::resetStopwatch(SuperTimer *pTimer)
{
    pTimer->setInitTimeMillis(0);
    pTimer->reset();
    pTimer->startPaused(true);
}

void Apps::stopwatch()
{
    // classic stopwatch
    long time_millis = 0;
    uint8_t timeDisplayShift = 0;

    if (this->app_init_edge)
    {
        resetStopwatch(&STOPWATCH_CHRONO_2);

        // chrono 1 contains the always-on timer (counting since box startup) at app init.
        STOPWATCH_CHRONO_1.setInitTimeMillis(always_on_timer.getTimeMillis());
        STOPWATCH_CHRONO_1.start();
    }

    // which chrono is loaded?
    if (binaryInputsToggleValue & (1 << BUTTON_INDEXED_SMALL_3))
    {
        pSsuperTimer = &STOPWATCH_CHRONO_1;
        pLongValue = &STOPWATCH_LAP_MEMORY_1;
    }
    else
    {
        pSsuperTimer = &STOPWATCH_CHRONO_2;
        pLongValue = &STOPWATCH_LAP_MEMORY_2;
    }

    time_millis = pSsuperTimer->getTimeMillis();
    if (binaryInputsEdgeUp & (1 << BUTTON_INDEXED_BIG_1))
    {
        // save and show laptime at press
        *pLongValue = time_millis;
    }

    bool paused = pSsuperTimer->getIsPaused();

    if (binaryInputsEdgeUp & (1 << BUTTON_INDEXED_BIG_2))
    {
        // set chronometer to zero
        pSsuperTimer->setInitTimeMillis(0);
        pSsuperTimer->startPaused(paused);
    }

    if (binaryInputsEdgeUp & (1 << BUTTON_INDEXED_BIG_3))
    {
        pSsuperTimer->paused(!paused);
    }
    if (!paused)
    {
        // if visible timer is not paused (aka running), the box should not auto power off.
        // chrono 1 initially contains the always on timer, but that's ok. If it's visible, and running, the box should not auto power off.
        resetInactivityTimer();
    }

    // if ((millis_quarter_second_period() && paused) || millis_half_second_period())

    if ((binaryInputsValue & (1 << BUTTON_INDEXED_BIG_0)) ||
        (binaryInputsValue & (1 << BUTTON_INDEXED_BIG_1)))
    {
        // show saved laptime at press
        time_millis = *pLongValue;
    }

    if (binaryInputsToggleValue & (1 << BUTTON_INDEXED_SMALL_2) || (time_millis > 9999000))
    {
        // normal clock with minutes and seconds
        displayTimerSecondsBlinker(pSsuperTimer);
        timeMillisToClockString(textBuf, time_millis);
    }
    else
    {
        // stopwatch display, with maximum accuracy. (accuracy depending on total time, showing as many decimals as possible)
        timeDisplayShift = 0;
        while (time_millis > 9999)
        {
            timeDisplayShift++;
            time_millis /= 10;
        }

        textBuf[0] = SPACE_FAKE_ASCII;
        textBuf[1] = SPACE_FAKE_ASCII;

        intToDigitsString(textBuf, time_millis, true);

        setDecimalPoint(true, timeDisplayShift);
    }

    // small button without a purpose
    lights &= ~(1 << LIGHT_BUTTON_SMALL_1);

    // alluring start/stop button blinking
    if ((millis_quarter_second_period() && paused) || (millis_second_period() && !paused))
    {
        lights |= 1 << LIGHT_BUTTON_BIG_3;
    }

    // lap time availablel
    lights |= (*pLongValue != 0) << LIGHT_BUTTON_BIG_0;

    textBufToDisplay();
}

void Apps::modeRandomWorld()
{
    if (this->app_init_edge)
    {
        randomWorldState = randomWorldIdle;
        randomModeTrigger(false);
#ifdef ENABLE_EEPROM
        RANDOMWORLD_UPPER_BOUNDARY_NUMBER_DRAW = eeprom_read_word((uint16_t *)EEPROM_RANDOM_WORLD_UPPER_BOUNDARY_NUMBER_DRAW);
        encoder_dial->setValue(RANDOMWORLD_UPPER_BOUNDARY_NUMBER_DRAW);
#else
        RANDOMWORLD_UPPER_BOUNDARY_NUMBER_DRAW = 10;
#endif
    }

    // textbuf contains the actual random generated graphics. Set to display at start, because it might be overriden in this routine.
    textBufToDisplay();

    switch (randomWorldState)
    {
    case randomWorldIdle:
    {
        if (binaryInputsToggleValue & (1 << BUTTON_INDEXED_SMALL_3))
        {
            uint16_t delay_seconds = dialGetIndexedtime();
            // set autoroll time.
            RANDOMWORLD_AUTODRAW_DELAY.setInitTimeMillis(-1000 * (long)delay_seconds);

            if (millis_blink_250_750ms())
            {
                setStandardTextToTextHANDLE(TEXT_AUTO);
            }
            else
            {
                ledDisp->setNumberToDisplayAsDecimal(delay_seconds);
            }
        }
        else
        {
            if (encoder_dial->getDelta())
            {
                randomWorldState = randomWorldRollingEnd;
            }
        }

#ifdef NICE_BUT_TAKES_MEMORY
        button_light_blink_quarter_second_period(lights_indexed[RANDOM_WORLD_ACTIVE_BIG_BUTTON_INDEX]);
#endif
        if (isBigButtonPressEdgeUpDetected())
        {
#ifdef NICE_BUT_TAKES_MEMORY
            RANDOM_WORLD_ACTIVE_BIG_BUTTON_INDEX = binaryInputsEdgeUpBigButtonIndex;
#endif
            RANDOMWORLD_RANDOM_TYPE = binaryInputsEdgeUpBigButtonIndex + 4 * ((binaryInputsToggleValue & (1 << BUTTON_INDEXED_SMALL_1)) > 0);
            randomWorldState = randomWorldRolling;

            // set up animation
            RANDOMWORLD_ROLL_SPEED.start(-30 - (((binaryInputsValue & (1 << BUTTON_INDEXED_BIG_2)) > 0) * 1970)); // special case for upper limit setting for random number.
        }
    }
    break;

    case randomWorldRolling:
    {
        // check state
        bool roll_end = false;

        // //if autoroll
        if (binaryInputsToggleValue & (1 << BUTTON_INDEXED_SMALL_3))
        {
            // autoroll no need for button
            roll_end = true;
        }
        else
        {
            // wait for button release

            // the following build up of the mask looks cumbersome, but, it's all done at precompiler time. , so it's just one byte of flash memory.
            // byte big_buttons_mask =
            //     1 << BUTTON_INDEXED_BIG_0 |
            //     1 << BUTTON_INDEXED_BIG_1 |
            //     1 << BUTTON_INDEXED_BIG_2 |
            //     1 << BUTTON_INDEXED_BIG_3;

            // if ((binaryInputsEdgeDown & big_buttons_mask) > 0)
            if ((binaryInputsEdgeDown & BIG_BUTTON_MASK) > 0)
            // if ((binaryInputsEdgeDown & (1 << BUTTON_INDEXED_BIG_0 | 1 << BUTTON_INDEXED_BIG_1 | 1 << BUTTON_INDEXED_BIG_2 | 1 << BUTTON_INDEXED_BIG_3)) > 0)
            {
                roll_end = true;
            }
        }

        if (roll_end)
        {
            randomWorldState = randomWorldRollingEnd;
        }

        // display
        if (binaryInputsToggleValue & (1 << BUTTON_INDEXED_SMALL_2))
        {
            // animated
            if (RANDOMWORLD_ROLL_SPEED.getCountDownTimerElapsedAndRestart())
            {
                buzzerPlayApproval();
                randomModeTrigger(false);
            }
        }
        else
        {
            // during roll all lights on
            ledDisp->setNumberToDisplayAsDecimal(8888);

            // check for continued key press at random number generator to activate settings menu
            if ((binaryInputsValue & (1 << BUTTON_INDEXED_BIG_2)) && (getCountDownTimerHasElapsed(&RANDOMWORLD_ROLL_SPEED)))
            {
                // hack to set upper limit for random number

                RANDOMWORLD_UPPER_BOUNDARY_NUMBER_DRAW = encoder_dial->getValueLimited(100, false);

                RANDOMWORLD_INDEX_FROM_BINGO = 0; // reset the bingo

                if (encoder_dial->getDelta())
                {
                    // for a more pleasant experience (no blinking during knob turning)
                    set_blink_offset();
                }

                if (millis_blink_250_750ms())
                {
                    setStandardTextToTextHANDLE(TEXT_SET);
                }
                else
                {
                    ledDisp->setNumberToDisplay(RANDOMWORLD_UPPER_BOUNDARY_NUMBER_DRAW, false);
                }
            }
        }
    }
    break;

    case randomWorldRollingEnd:
    {
        if (binaryInputsToggleValue & (1 << BUTTON_INDEXED_SMALL_2))
        {
            if (RANDOMWORLD_ROLL_SPEED.getCountDownTimerElapsedAndRestart())
            {
                buzzerPlayApproval();
                randomModeTrigger(false);

                // roll slower and slower until threshold reached.
                RANDOMWORLD_ROLL_SPEED.setInitTimeMillis(RANDOMWORLD_ROLL_SPEED.getInitTimeMillis() * 1.4);
                if (RANDOMWORLD_ROLL_SPEED.getInitTimeMillis() < -600)
                {
                    randomWorldState = randomWorldShowResult;
                }
            }
        }
        else
        {
#ifdef ENABLE_EEPROM
            // save to eeprom
            eeprom_update_word((uint16_t *)EEPROM_RANDOM_WORLD_UPPER_BOUNDARY_NUMBER_DRAW, RANDOMWORLD_UPPER_BOUNDARY_NUMBER_DRAW); // eeprom_update_... only writes if different from what's in address, no need to read to check.
#endif

            randomWorldState = randomWorldShowResult;
            buzzerPlayApproval();
        }
    }
    break;

    case randomWorldShowResult:
    {
        randomModeTrigger(true);
        if (binaryInputsToggleValue & (1 << BUTTON_INDEXED_SMALL_3))
        {
            // auto roll delay.
            RANDOMWORLD_AUTODRAW_DELAY.start();
            randomWorldState = randomWorldAutoRollDelay;
        }
        else
        {
            randomWorldState = randomWorldIdle;
        }
    }
    break;

    case randomWorldAutoRollDelay:
    {
        if (getCountDownTimerHasElapsed(&RANDOMWORLD_AUTODRAW_DELAY))
        {
            // set up animation
            RANDOMWORLD_ROLL_SPEED.start(-30);

            randomWorldState = randomWorldRolling;
        }
        if (!(binaryInputsToggleValue & (1 << BUTTON_INDEXED_SMALL_3)))
        {
            randomWorldState = randomWorldIdle;
        }
#ifdef NICE_BUT_TAKES_MEMORY
        lights |= 1 << lights_indexed[RANDOM_WORLD_ACTIVE_BIG_BUTTON_INDEX];
#endif
    }

    break;
    }
}

void Apps::randomModeTrigger(bool forReal)
{
    // set the textBuf.

    // forReal: if false, just for animations. Important for e.g. drawing a card from the deck. During animations, we're not really drawing a card from the deck.

    const int16_t randomUpperLimits[8] = {6, 26, RANDOMWORLD_UPPER_BOUNDARY_NUMBER_DRAW, 2, 6, 52, RANDOMWORLD_UPPER_BOUNDARY_NUMBER_DRAW, 2};

    RANDOMWORLD_RANDOM_NUMBER = random(0, randomUpperLimits[RANDOMWORLD_RANDOM_TYPE]);

    ledDisp->blanksToBuf(textBuf);

    switch (RANDOMWORLD_RANDOM_TYPE)
    {
    case RANDOMWORLD_ROLLONEDICE:
    {
        for (uint8_t i = 0; i < 4; i++)
        {
            textBuf[i] = pgm_read_byte_near(dice_eyes_display + RANDOMWORLD_RANDOM_NUMBER * 4 + (i)); //* 4 --> 4 bytes per dword
        }
    }
    break;

    case RANDOMWORLD_ROLLFOURDICE:
    {
        // throw four dice
        for (uint8_t i = 0; i < 4; i++)
        {
            textBuf[i] = random(49, 55); // char 1 to 6
        }
    }
    break;

    case RANDOMWORLD_RANDOMLETTER:
    {
        // show letter alphabeth, plus its position.
        // displayLetterAndPositionInAlphabet(textBuf, RANDOMWORLD_RANDOM_NUMBER);

        displayLetterAndPositionInAlphabet(textBuf, (int16_t)weightedRandomLetter());
        // numberToBufAsDecimal((int16_t)weightedRandomLetter());
    }
    break;

    case RANDOMWORLD_TAKERANDOMCARDFROMDECK:
    {
        if (!forReal)
        {
            // don't draw a card if it's not for real. We will not even display a card, as that would be confusing. Just show blanks.
            break;
        }

        RANDOMWORLD_RANDOM_NUMBER = bingo(&RANDOMWORLD_INDEX_FROM_RANDOM_IN_A_BAG, CARDS_DECK, 52);

        // show playing card
        if (RANDOMWORLD_RANDOM_NUMBER % 13 < 9)
        {
            textBuf[1] = RANDOMWORLD_RANDOM_NUMBER % 13 + 49;
        }
        else
        {
            textBuf[0] = 49;                                                       // 1
            textBuf[1] = (3 - (((RANDOMWORLD_RANDOM_NUMBER) % 13) + 1) % 10) + 48; // 9,10,11,13 to char 0 1 2 3
        }

        char test[4] = {'H', 'D', 'S', 'C'};
        textBuf[3] = test[RANDOMWORLD_RANDOM_NUMBER / 13];
    }

    break;

    case RANDOMWORLD_BINGO:
    {
        if (!forReal)
        {
            // dont draw if not for real
            break;
        }
        RANDOMWORLD_RANDOM_NUMBER = bingo(&RANDOMWORLD_INDEX_FROM_BINGO, BINGO_NUMBERS_LIST, RANDOMWORLD_UPPER_BOUNDARY_NUMBER_DRAW);
    }
    // NO BREAK HERE we just changed the random number to a part of a raffle draw.
    case RANDOMWORLD_RANDOMNUMBER:
    {
        // random number
        numberToBufAsDecimal(RANDOMWORLD_RANDOM_NUMBER + 1);
    }
    break;

    case RANDOMWORLD_HEADSORTAILS:
    // NO BREAK HERE, we will overflow to yes no, but change the text. DAngereous I know. But, we need the extra bytes.
    case RANDOMWORLD_YESORNO:
    {
        setStandardTextToTextBuf(60 +                                // offset in standardtexts
                                 RANDOMWORLD_RANDOM_NUMBER * 4 +     // value , 4 chars more or not? yes vs no text, tails vs heads text
                                 (RANDOMWORLD_RANDOM_TYPE - 3) * 2); // text type: yes/no or heads/tails
    }
    break;
    }
}

void Apps::modeSettings()
{
#ifdef ENABLE_SELECT_APPS_WITH_SELECTOR
#ifdef ENABLE_SOFT_POWER_OFF
    const uint8_t analog_input_pins[4] = {PIN_SELECTOR_DIAL, PIN_BUTTONS_SMALL, PIN_BUTTONS_BIG, PIN_POWER_ON_HOLD};
#else
    const uint8_t analog_input_pins[4] = {PIN_SELECTOR_DIAL, PIN_BUTTONS_SMALL, PIN_BUTTONS_BIG, PIN_MERCURY_SWITCHES};

#endif
#else
    const uint8_t analog_input_pins[2] = {PIN_BUTTONS_SMALL, PIN_BUTTONS_BIG};
#endif
    if (this->app_init_edge)
    {
    }

    // back and forth motion required of the potentio to count up modes
    if ((encoder_dial->getDelta() < 0 && MODE_SETTINGS_SELECTOR % 2 == 0))
    {
        MODE_SETTINGS_SELECTOR++;
    }
    else if (encoder_dial->getDelta() > 0 && MODE_SETTINGS_SELECTOR % 2 != 0)
    {
        MODE_SETTINGS_SELECTOR++;
    }

    setStandardTextToTextBuf(TEXT_SPACES);

    if (MODE_SETTINGS_SELECTOR < 6)
    {
        // normal mode

        // simple repetitive, predictive mode.
        // each button triggers its corresponding light.
        // potentio sets display brightness
        // no buzzer
        // display lights up a segment for each button.

        for (uint8_t i = 0; i < 4; i++)
        {

            // every big button has a matching small button assigned
            if (binaryInputsToggleValue & (1 << (i + 4))) // small button as l atching button
            {
                // big button pressed while its matching small button is ON?

                if (binaryInputsValue & (1 << i))
                {
                    textHandle[i] = '8';
                }
                else
                {
                    textHandle[i] = ONLY_MIDDLE_SEGMENT_FAKE_ASCII;
                }
            }
            else if (binaryInputsValue & (1 << i))
            {
                textHandle[i] = '0';
            }
        }

        if (millis_quarter_second_period())
        { // BAD PRACTICE GIVES FUN RESULTS. Will go through this loop continuously when true (no edge detection). And then half a second static. I kind of like the effect
            MODE_SETTINGS_DECIMAL_POINT_COUNTER++;
            if (MODE_SETTINGS_DECIMAL_POINT_COUNTER > 15)
            {
                MODE_SETTINGS_DECIMAL_POINT_COUNTER = 0;
            }
        }
        ledDisp->setDecimalPointsToDisplay(MODE_SETTINGS_DECIMAL_POINT_COUNTER);
    }
    else if (MODE_SETTINGS_SELECTOR < 8)
    {
        // enable/disable sound

        lights |= 1 << LIGHT_BUTTON_BIG_0;
        if (binaryInputsEdgeUp & (1 << BUTTON_INDEXED_BIG_0))
        {
#ifdef ENABLE_EEPROM

            eeprom_update_byte(
                (uint8_t *)EEPROM_SOUND_DISABLED,
                !eeprom_read_byte((uint8_t *)EEPROM_SOUND_DISABLED)); // eeprom_update_... only writes if different from what's in address, no need to read to check.
#endif

            if (buzzer->getPin() == PIN_BUZZER)
            {
                buzzer->setPin(PIN_BUZZER_FAKE);
            }
            else
            {
                buzzer->setPin(PIN_BUZZER);
            }
        }

        // menu title
        setStandardTextToTextBuf(TEXT_BEEP);

        // value text
        uint8_t text = TEXT_YES;
        if (buzzer->getPin() == PIN_BUZZER)
        {
            text = TEXT_NO;
        }
        setStandardTextToTextHANDLE(text);
    }
    else if (MODE_SETTINGS_SELECTOR < 10)
    {
#ifdef ENABLE_BATTERY_STATUS

        ledDisp->setNumberToDisplayAsDecimal((int16_t)batteryVoltage);
        // menu title
        setStandardTextToTextBuf(TEXT_BATTERY);

#endif
    }

#ifdef ENABLE_SOFT_POWER_OFF
    else if (MODE_SETTINGS_SELECTOR < 12)
    {
        // enable/disable auto power off

        lights |= 1 << LIGHT_BUTTON_BIG_0;

        uint8_t auto_power_off_enabled = true;
        if (binaryInputsEdgeUp & (1 << BUTTON_INDEXED_BIG_0))
        {
#ifdef ENABLE_EEPROM

            eeprom_update_byte(
                (uint8_t *)EEPROM_LUCIEBOX_AUTO_POWER_OFF_DISABLED,
                !eeprom_read_byte((uint8_t *)EEPROM_LUCIEBOX_AUTO_POWER_OFF_DISABLED));
        } // eeprom_update_... only writes if different from what's in address, no need to read to check.

        auto_power_off_enabled = (eeprom_read_byte((uint8_t *)EEPROM_LUCIEBOX_AUTO_POWER_OFF_DISABLED) != 0); // eeprom_update_... only writes if different from what's in address, no need to read to check.
#endif

        // menu title
        setStandardTextToTextBuf(TEXT_AUTO);

        // value text
        uint8_t text = TEXT_NO;
        if (auto_power_off_enabled)
        {
            text = TEXT_YES;
        }
        setStandardTextToTextHANDLE(text);
    }

#endif

    else if (MODE_SETTINGS_SELECTOR < 20)
    {

#ifdef ENABLE_SELECT_APPS_WITH_SELECTOR
        // A0 handles the selector button analog input. It will not change apps when the selector knob is rotated in this menu.
        // menu title
        textBuf[2] = 'A';
        uint8_t index = (MODE_SETTINGS_SELECTOR - 10) / 2;
        ledDisp->digitValueToChar(&textBuf[3], index);

        // Value
        if (millis_blink_250_750ms())
        {
            // be stable when shown (only measure when menu text is shown)
            SETTINGS_MODE_ANALOG_VALUE = (int16_t)analogRead(analog_input_pins[index]);
        }
        ledDisp->setNumberToDisplayAsDecimal(SETTINGS_MODE_ANALOG_VALUE);
#else

        // menu title
        // represents the analog value, which stands for which big buttons, or small buttons are pressed.
        textBuf[2] = 'B';
        uint8_t index = MODE_SETTINGS_SELECTOR % 2;
        ledDisp->digitValueToChar(&textBuf[3], index);

        // Value
        if (millis_blink_250_750ms())
        {
            // be stable when shown (only measure when menu text is shown)
            SETTINGS_MODE_ANALOG_VALUE = (int16_t)analogRead(analog_input_pins[index]);
        }
        ledDisp->setNumberToDisplayAsDecimal(SETTINGS_MODE_ANALOG_VALUE);
#endif
    }
    else if (MODE_SETTINGS_SELECTOR < 22)
    {
        // show luciebox firmware version number
        // menu title

        // value
        ledDisp->setNumberToDisplayAsDecimal(SOFTWARE_VERSION);
        textHandle[0] = 'F'; // v doesn't work. So, F from Firmware version it is.
    }
    else if (MODE_SETTINGS_SELECTOR < 24)
    {
// display amount of times the luciebox was used
// menu value
#ifdef ENABLE_EEPROM
        ledDisp->setNumberToDisplayAsDecimal(eeprom_read_word((uint16_t *)EEPROM_LUCIEBOX_POWER_CYCLE_COUNTER));
#else
        ledDisp->setNumberToDisplayAsDecimal(666);
#endif
        // menu title
        setStandardTextToTextBuf(TEXT_QUANTITY);
    }
    else if (MODE_SETTINGS_SELECTOR < 26)
    {
        lights |= 1 << LIGHT_BUTTON_BIG_0;
        if (binaryInputsValue & (1 << BUTTON_INDEXED_BIG_0))
        {
#ifdef ENABLE_EEPROM
            // lights |= 1 << LIGHT_BUTTON_BIG_2; // will erase all user program memory. Purposly don't advertise
            lights |= 1 << LIGHT_BUTTON_BIG_3; // erases only high scores in games. Which is nice if you want to have a fresh start for a nice gamenight of "Lucieboxes and booz"
            if (binaryInputsEdgeUp & (1 << BUTTON_INDEXED_BIG_2))
            {
                this->eraseEepromRangeLimited(EEPROM_USER_RESET);
            }
            if (binaryInputsEdgeUp & (1 << BUTTON_INDEXED_BIG_3))
            {
                this->eraseEepromRangeLimited(EEPROM_APP_SETTINGS_RESET);
            }
#endif
        }
        else
        {
            setStandardTextToTextBuf(TEXT_RESET);
        }
    }
    else if (MODE_SETTINGS_SELECTOR < 28)
    {
        // measure cycle time.
        // 2021-10-02: between 800 and 1200 millis per cycle.
        // if (MODE_SETTINGS_CYCLE_TIMING_INDEX == 0){
        // MODE_SETTINGS_CYCLE_TIMING_INDEX ++;
        // MODE_SETTINGS_CYCLE_TIMING_MILLIS = micros();

        // }else if (MODE_SETTINGS_CYCLE_TIMING_INDEX == 1){
        // MODE_SETTINGS_CYCLE_TIMING_INDEX ++;
        // MODE_SETTINGS_CYCLE_TIMING_MILLIS_2 = micros();

        // }else{
        // MODE_SETTINGS_CYCLE_TIMING_INDEX = 0;
        // #ifdef ENABLE_SERIAL
        // Serial.println("---");
        // Serial.println(MODE_SETTINGS_CYCLE_TIMING_MILLIS);

        // Serial.println(MODE_SETTINGS_CYCLE_TIMING_MILLIS_2);
        // Serial.println(MODE_SETTINGS_CYCLE_TIMING_MILLIS_2 - MODE_SETTINGS_CYCLE_TIMING_MILLIS);
        // #endif
        // }
    }
    else
    {
        ledDisp->setNumberToDisplayAsDecimal(MODE_SETTINGS_SELECTOR);
    }

    if (MODE_SETTINGS_SELECTOR >= 6)
    {
        // originally: show values one seconds, menu items half a second
        // in luciebox settings mode
        if (millis_blink_250_750ms())
        {
            textBufToDisplay();

#ifdef ENABLE_BATTERY_STATUS
            // atmega328p
            ADMUX = _BV(REFS0) | _BV(MUX3) | _BV(MUX2) | _BV(MUX1);
            //  ADMUX = bit (REFS0) | bit (REFS1);  // Internal 1.1V reference
            // delay(2); // Wait for Vref to settle

            loadBuzzerTrack(SONG_ALPHABET);
            buzzerSilentClearBuffer();
            buzzerChangeSpeedRatioWithEncoderDial();

            // Serial.println(SETTINGS_APP_BATTERY_VOLTAGE);
            ADCSRA |= _BV(ADSC); // Start conversion
            while (bit_is_set(ADCSRA, ADSC))
                ; // measuring

            uint8_t low = ADCL;  // must read ADCL first - it then locks ADCH
            uint8_t high = ADCH; // unlocks both

            long result = (high << 8) | low;

            result = 1125300L / result; // Calculate Vcc (in mV); 1125300 = 1.1*1023*1000

            batteryVoltage = result;

#endif
        }
    }
}

void Apps::eraseEepromRangeLimited(uint8_t setting)
{
#ifdef ENABLE_EEPROM
    uint16_t first = 0;
    if (setting == EEPROM_APP_SETTINGS_RESET)
    {
        first = EEPROM_FIRST_ADDRESS_APP_SETTINGS_RESET;
    }

    else if (setting == EEPROM_USER_RESET)
    {
        first = EEPROM_FIRST_ADDRESS_OF_USER_RANGE;
    }
    // else if (setting == EEPROM_TOTAL_RESET) // start from 0 to end
    // {
    // }

    for (uint16_t i = first; i <= EEPROM_LAST_ADDRESS; i++)
    {
        uint8_t erase_value = 0;

        if (i >= EEPROM_SEQUENCER_SONGS_START_ADDRESS && i < EEPROM_PICTURES_START_ADDRESS)
        {
            erase_value = 0xff;
        }

        eeprom_update_byte(
            (uint8_t *)i,
            erase_value); // eeprom_update_... only writes if different from what's in address, no need to read to check.
    }
    // playSongHappyDryer(); // do it, but no memory left.

#endif
}

void Apps::displayLetterAndPositionInAlphabet(char *textBuf, int16_t letterValueAlphabet)
{
    if (letterValueAlphabet > 8)
    {
        ledDisp->digitValueToChar(&textBuf[0], (letterValueAlphabet + 1) / 10);
    }
    ledDisp->digitValueToChar(&textBuf[1], (letterValueAlphabet + 1) % 10);

    textBuf[3] = letterValueAlphabet + 65; // show letters alphabet.
}

#ifdef ENABLE_TALLY_KEEPER
#ifdef ENABLE_EEPROM // tallies are kept in eeprom. No local record. So: no eeprom, no score keeping thank you. (this saved on memory)
void Apps::modeTallyKeeper()
{
    if (this->app_init_edge)
    {
    }

    // resetInactivityTimer(); // all score changes are written in eeprom. No more need to panic if box switches off.  // don't switch box off when displaying score!! --> controversial. Maybe it should then just beep every ten minutes?!

    // stage the score in the 'delta'
    if ((binaryInputsEdgeUp & (1 << BUTTON_INDEXED_SMALL_2)))
    {
        TALLY_KEEPER_DELTA--;
        set_blink_offset();
    }
    if ((binaryInputsEdgeUp & (1 << BUTTON_INDEXED_SMALL_3)))
    {
        TALLY_KEEPER_DELTA++;
        set_blink_offset();
    }
    int8_t step = encoder_dial->getDelta();
    if (step)
    {
        TALLY_KEEPER_DELTA += step;
        set_blink_offset();
    }

    // commit score to a certain tally
    if (isBigButtonPressEdgeUpDetected())
    {
        if (binaryInputsToggleValue & (1 << BUTTON_INDEXED_SMALL_1) && TALLY_KEEPER_DELTA == 0)
        {
            TALLY_KEEPER_DELTA = 1;
        }

        TALLY_KEEPER_ACTIVE_SCORE_INDEX = binaryInputsEdgeUpBigButtonIndex;
        int16_t score = getTallyScore(TALLY_KEEPER_ACTIVE_SCORE_INDEX);

        score += TALLY_KEEPER_DELTA;

        setTallyScore(TALLY_KEEPER_ACTIVE_SCORE_INDEX, score);

        if (TALLY_KEEPER_DELTA)
        {
            buzzerPlaySpecial();
        }
        else
        {
            buzzerPlayApproval();
        }

        TALLY_KEEPER_DELTA = 0;
        TALLY_RESET_SCORES_TIMER.start(TALLY_RESET_SCORES_TIMEOUT_MILLIS);
    }

    // reset certain tally
    if (getCountDownTimerHasElapsed(&TALLY_RESET_SCORES_TIMER))
    {
        if (binaryInputsValue & (1 << TALLY_KEEPER_ACTIVE_SCORE_INDEX))
        {
            // long press resets score.
            setTallyScore(TALLY_KEEPER_ACTIVE_SCORE_INDEX, 0);
            buzzerPlayDisappointment();
            TALLY_KEEPER_DELTA = 0; // if delta displayed, it can confuse people figuring out how it works. Long press should always mean: set it all to zero!
        }
    }

    // display functionality
    if (TALLY_KEEPER_DELTA != 0)
    {
        // if(millis_half_second_period())
        if (millis_blink_250_750ms())
        {
            setStandardTextToTextHANDLE(TEXT_SET);
            lights |= 1 << LIGHT_BUTTON_BIG_0 | 1 << LIGHT_BUTTON_BIG_1 | 1 << LIGHT_BUTTON_BIG_2 | 1 << LIGHT_BUTTON_BIG_3; // big button lights on
        }
        else
        {
            ledDisp->setNumberToDisplayAsDecimal(TALLY_KEEPER_DELTA);
        }
        lights |= 1 << LIGHT_BUTTON_SMALL_2 | 1 << LIGHT_BUTTON_SMALL_3;
        // lights &= ~BIG_BUTTON_MASK; // big button lights off.
        // button_light_blink_quarter_second_period(LIGHT_BUTTON_SMALL_3);
        // button_light_blink_quarter_second_period(LIGHT_BUTTON_SMALL_2);
    }
    else
    {
        int16_t display_value = getTallyScore(TALLY_KEEPER_ACTIVE_SCORE_INDEX);
        ledDisp->setNumberToDisplayAsDecimal(display_value);
        lights |= 1 << lights_indexed[TALLY_KEEPER_ACTIVE_SCORE_INDEX];
        lights &= ~(1 << LIGHT_BUTTON_SMALL_2 | 1 << LIGHT_BUTTON_SMALL_3);
    }
}

int16_t Apps::getTallyScore(uint8_t tally_index)
{
    return (int16_t)eeprom_read_word(EEPROM_TALLY_KEEPER_SCORES + 2 * tally_index);
}

void Apps::setTallyScore(uint8_t tally_index, int16_t value)
{
    eeprom_update_word(
        EEPROM_TALLY_KEEPER_SCORES + 2 * tally_index,
        value);
}

#endif
#endif

#ifdef ENABLE_SHOOTOUT
void Apps::shootout()
{
    if (this->app_init_edge)
    {

        SHOOTOUT_RANDOM_WAIT_TIME_MAX_INDEX = SHOOTOUT_DEFAULT_WAIT_TIME_INDEX;
        shootoutState = shootoutInitWait;
    }

    lights = 0;

    lights |= 1 << LIGHT_BUTTON_SMALL_3;

    if (binaryInputsToggleValue & (1 << BUTTON_INDEXED_SMALL_2))
    {

        lights |= 1 << LIGHT_BUTTON_SMALL_2;
    }

    if (SHOOTOUT_RANDOM_WAIT_TIME_MAX_INDEX != SHOOTOUT_DEFAULT_WAIT_TIME_INDEX)
    {
        lights |= 1 << LIGHT_BUTTON_SMALL_1;
    }

    switch (shootoutState)
    {
    case shootoutInitWait:
    {
        if (binaryInputsEdgeUp & (1 << BUTTON_INDEXED_SMALL_3))
        {

            if (!SHOOTOUT_GAME_ALREADY_STARTED)
            {
                // start of new game
                SHOOTOUT_GAME_ALREADY_STARTED = true;
                SHOOTOUT_END_GAME_WINNER_DISPLAY = false;
                for (uint8_t i = 0; i < BIG_BUTTONS_COUNT; i++)
                {
                    SHOOTOUT_SCORE[i] = 0;
                }
                loadBuzzerTrack(SONG_ATTACK);
            }
            shootoutState = shootoutInitRandomTime;
        }
        // if (this->millis_half_second_period())
        // {
        //     lights &= ~(1 << LIGHT_BUTTON_SMALL_3);
        //     // lights |= 1 << LIGHT_BUTTON_SMALL_3;

        // }

        lights &= ~(1 << LIGHT_BUTTON_SMALL_3); // small button 3 on by default, so switch off here.
        button_light_blink_half_second_period(LIGHT_BUTTON_SMALL_3);

        if (binaryInputsValue & (1 << BUTTON_INDEXED_SMALL_1))
        {
            // SHOOTOUT_MAX_RANDOM_WAIT_TIME = -20000; // great crazy long time.
            encoderDialRefreshTimeIndex(&SHOOTOUT_RANDOM_WAIT_TIME_MAX_INDEX);
        }
        SHOOTOUT_RANDOM_WAIT_TIME_MAX_SECONDS = indexToTimeSeconds(SHOOTOUT_RANDOM_WAIT_TIME_MAX_INDEX);
    }
    break;
    case shootoutWaitForQuizmaster:
    {
        if (binaryInputsEdgeUp & (1 << BUTTON_INDEXED_SMALL_3))
        {
            shootoutState = shootoutInitWait;
        }
    }
    break;

    case shootoutInitRandomTime:
    {
        shootoutState = shootoutWaitRandomTime;
        SHOOTOUT_RANDOM_WAIT_TIME.start(random((long)-1000 * SHOOTOUT_RANDOM_WAIT_TIME_MAX_SECONDS, (long)-500));
    }

    case shootoutWaitRandomTime:
    {
        if (getCountDownTimerHasElapsed(&SHOOTOUT_RANDOM_WAIT_TIME))
        {
            // //TEST SHOW RAW ANALOG VALUES
            // //empty analog input buffer
            // for(uint8_t i=0;i<100;i++){
            // 	SHOOTOUT_ANALOG_VALUES_CHECK[i] = 0;
            // }
            // SHOOTOUT_ANALOG_INPUT_SAMPLE_INDEX = 0;
            // //ENDTEST

            SHOOTOUT_FIRST_ANALOG_BIG_BUTTON_NON_ZERO_VALUE = 0;
#ifdef ENABLE_SERIAL
            SHOOTOUT_RECORDING_INDEX = 0;
#endif
            shootoutState = shootoutWaitPlayerPress;
        }

        // check here, any player pressing his button = score to zero.
        if (isBigButtonPressEdgeUpDetected())
        {
            SHOOTOUT_SCORE[binaryInputsEdgeUpBigButtonIndex] = 0;
            buzzerPlayDisappointment();
        }

#ifndef ENABLE_SELECT_APPS_WITH_SELECTOR
        if (binaryInputsEdgeUp & (1 << BUTTON_INDEXED_SMALL_3))
        {
            SHOOTOUT_GAME_ALREADY_STARTED = false;
            shootoutState = shootoutInitWait;
        }
#endif
    }
    break;

    case shootoutWaitPlayerPress:
    {
        // //TEST SHOW RAW ANALOG VALUES
        // SHOOTOUT_ANALOG_VALUES_CHECK[SHOOTOUT_ANALOG_INPUT_SAMPLE_INDEX] = analogRead(PIN_BUTTONS_BIG)/4;
        // nextStepRotate(&SHOOTOUT_ANALOG_INPUT_SAMPLE_INDEX,true,0,99);
        // //ENDTEST

        // 16,32,64,128 are the stored values of the individual raw big buttons (analog / 4)   64, 128, 256, 512
        uint8_t bigButtonAnalogRaw = analogRead(PIN_BUTTONS_BIG) / 4;
        if (bigButtonAnalogRaw > 3 && SHOOTOUT_FIRST_ANALOG_BIG_BUTTON_NON_ZERO_VALUE == 0)
        {
            SHOOTOUT_FIRST_ANALOG_BIG_BUTTON_NON_ZERO_VALUE = bigButtonAnalogRaw;
        }

        // record the first 100 cycles after analog is non zero. Interesting to see how the values fluctuate at the very start.
#ifdef ENABLE_SERIAL
        if (SHOOTOUT_RECORDING_INDEX < 100 && SHOOTOUT_FIRST_ANALOG_BIG_BUTTON_NON_ZERO_VALUE != 0)
        {
            SHOOTOUT_ANALOG_BUTTONS_RECORDING[SHOOTOUT_RECORDING_INDEX] = bigButtonAnalogRaw;
            SHOOTOUT_RECORDING_INDEX++;
        }
#endif

        byte big_buttons_lights = 1 << LIGHT_BUTTON_BIG_0 | 1 << LIGHT_BUTTON_BIG_1 | 1 << LIGHT_BUTTON_BIG_2 | 1 << LIGHT_BUTTON_BIG_3;
        lights |= big_buttons_lights;

        // uint8_t compare_values [4];

        if (isBigButtonPressEdgeUpDetected())
        {

            // set the theoretical analog value for the detected button
            // SHOOTOUT_ANALOG_VALUES_CHECK[binaryInputsEdgeUpBigButtonIndex] = 0x10 << binaryInputsEdgeUpBigButtonIndex; // (0x10=16) button 0:16, 1:32, 2:64, 3:128

            // go to next state

            // run through the four big buttons.
            for (int big_button_index = 0; big_button_index < 4; big_button_index++)
            {
                // IF the button is indicated as pressed, this button is in the running to be the first press (will then be compared with the first analog value that was detected. If multiple button presses are deteced, we will then check who was pressing first.)
                if (binaryInputsValue & (1 << big_button_index))
                {
                    SHOOTOUT_ANALOG_VALUES_CHECK[big_button_index] = 0x10 << big_button_index; // theoretical value per button. // (0x10=16) button 0:16, 1:32, 2:64, 3:128
                }
                else
                {
                    SHOOTOUT_ANALOG_VALUES_CHECK[big_button_index] = 255; // biggest number, trying to be unobtainable value to get this button out of the way.
                }
            }

            shootoutState = shootoutDefineRoundWinner;
        }

        // if (isBigButtonPressEdgeUpDetected())
        // {
        //     SHOOTOUT_ANALOG_VALUES_CHECK[binaryInputsEdgeUpBigButtonIndex] = 0x10 << binaryInputsEdgeUpBigButtonIndex; // (0x10=16) button 0:16, 1:32, 2:64, 3:128

        //     // go to next state
        //     shootoutState = shootoutDefineRoundWinner;
        // }
        // else
        // {
        //     SHOOTOUT_ANALOG_VALUES_CHECK[binaryInputsEdgeUpBigButtonIndex] = 255; // unobtainable value. maximum.
        // }

        // if (!(binaryInputsToggleValue & (1 << BUTTON_INDEXED_SMALL_3)))
        // {
        //     shootoutState = shootoutWaitForQuizmaster;
        // }
        // //TEST SHOW RAW ANALOG VALUES
        // Serial.println("---");
        // Serial.println(SHOOTOUT_ANALOG_INPUT_SAMPLE_INDEX);
        // //display recorded values
        // uint8_t first_non_zero_value = 0;
        // for(uint8_t i=0;i<100;i++){
        // 	Serial.println(SHOOTOUT_ANALOG_VALUES_CHECK[SHOOTOUT_ANALOG_INPUT_SAMPLE_INDEX]);
        // 	// if (first_non_zero_value == 0){
        // 	// 	first_non_zero_value = SHOOTOUT_ANALOG_VALUES_CHECK[SHOOTOUT_ANALOG_INPUT_SAMPLE_INDEX];
        // 	// }
        // 	nextStepRotate(&SHOOTOUT_ANALOG_INPUT_SAMPLE_INDEX,true,0,99);
        // }
        // //ENDTEST

        if (binaryInputsEdgeUp & (1 << BUTTON_INDEXED_SMALL_3))
        {
            SHOOTOUT_GAME_ALREADY_STARTED = false;
            shootoutState = shootoutInitWait;
        }
    }
    break;

    case shootoutDefineRoundWinner:
    {
        // Which theoretical button value is the closest to the first detected analog value? That's the winner. It looks pretty sound after some experimentation.

        // calculate diffs and put them a bit further in the array.
        for (uint8_t i = 0; i < 4; i++)
        {
            // check difference of theoretical value with first detected actual analog value.
            SHOOTOUT_ANALOG_VALUES_CHECK[4 + i] = abs(SHOOTOUT_FIRST_ANALOG_BIG_BUTTON_NON_ZERO_VALUE - SHOOTOUT_ANALOG_VALUES_CHECK[i]);
        }

        // get button index with smallest diff (which is the winner)
        SHOOTOUT_MOST_RECENT_ROUND_WINNER_INDEX = 0;
        uint8_t smallestDiff = 255;
        for (uint8_t i = 0; i < 4; i++)
        {
            if (SHOOTOUT_ANALOG_VALUES_CHECK[4 + i] < smallestDiff)
            {
                SHOOTOUT_MOST_RECENT_ROUND_WINNER_INDEX = i;
                smallestDiff = SHOOTOUT_ANALOG_VALUES_CHECK[4 + i];
            }
        }

#ifdef ENABLE_SERIAL
        // TEST SHOW RAW ANALOG VALUES
        Serial.println("start");
        for (uint8_t i = 0; i < 8; i++)
        {
            Serial.println(SHOOTOUT_ANALOG_VALUES_CHECK[i]);
        }
        Serial.println(SHOOTOUT_FIRST_ANALOG_BIG_BUTTON_NON_ZERO_VALUE);
        Serial.println(SHOOTOUT_MOST_RECENT_ROUND_WINNER_INDEX);

        Serial.println("replay:");
        for (uint8_t i = 0; i < 100; i++)
        {
            Serial.println(SHOOTOUT_ANALOG_BUTTONS_RECORDING[i]);
        }
        Serial.println("end");
#endif
        // //ENDTEST
        SHOOTOUT_SCORE_MEMORY = SHOOTOUT_SCORE[SHOOTOUT_MOST_RECENT_ROUND_WINNER_INDEX];

        shootoutState = shootoutRoundAfterMath;
    }
    break;

    case shootoutRoundAfterMath:
    {
        // set score with the dial if in quiz mode (in quiz mode, you might be first to press a button, but not know the answer...)
        int16_t score = (int16_t)SHOOTOUT_SCORE[SHOOTOUT_MOST_RECENT_ROUND_WINNER_INDEX];
        stepChange(&score, encoder_dial->getDelta(), 0, 10, false);

        if (!(binaryInputsToggleValue & (1 << BUTTON_INDEXED_SMALL_2)))
        {
            // shoot out mode
            initiateCountDowntimerWith500Millis(&SHOOTOUT_RANDOM_WAIT_TIME);
            score++;
            shootoutState = shootoutRecoverDelayForAutoNextRound;
        }

#ifdef ENABLE_SELECT_APPS_WITH_SELECTOR
        else if (!(binaryInputsValue & (1 << BUTTON_INDEXED_SMALL_3)))
        {
            shootoutState = shootoutWaitForQuizmaster;
        }
#else
            else if (binaryInputsEdgeUp & (1 << BUTTON_INDEXED_SMALL_3))
            {
                // SHOOTOUT_GAME_ALREADY_STARTED = false;
                shootoutState = shootoutInitWait;
            }
#endif

        SHOOTOUT_SCORE[SHOOTOUT_MOST_RECENT_ROUND_WINNER_INDEX] = (uint8_t)score;
        if (score > 9) // magic number, but good number
        {
            SHOOTOUT_SCORE[SHOOTOUT_MOST_RECENT_ROUND_WINNER_INDEX]--; // let's not show a ten on the display (it messes up the single digit mode.)
            SHOOTOUT_END_GAME_WINNER_DISPLAY = true;
            playSongHappyDryer();
            SHOOTOUT_GAME_ALREADY_STARTED = false;
            shootoutState = shootoutInitWait;
        }
    }
    break;

    case shootoutRecoverDelayForAutoNextRound:
    {
        if (getCountDownTimerHasElapsed(&SHOOTOUT_RANDOM_WAIT_TIME))
        {
            shootoutState = shootoutInitRandomTime;
        }
    }
    break;
    }

    int16_t scoreToDisplay = 10000; // 10000 to make sure there will always be zeros for all digits
    int16_t multiplier = 1000;
    for (uint8_t i = 0; i < BIG_BUTTONS_COUNT; i++)
    {
        scoreToDisplay += multiplier * (SHOOTOUT_SCORE[i]);
        multiplier /= 10;
    }
    ledDisp->setNumberToDisplayAsDecimal(scoreToDisplay);

    if (SHOOTOUT_END_GAME_WINNER_DISPLAY)
    {
        textHandle[SHOOTOUT_MOST_RECENT_ROUND_WINNER_INDEX] = '?';
    }

    if (millis_quarter_second_period() && shootoutState == shootoutRoundAfterMath)
    {
        textHandle[SHOOTOUT_MOST_RECENT_ROUND_WINNER_INDEX] = ' ';
    }

    if (binaryInputsValue & (1 << BUTTON_INDEXED_SMALL_1) && shootoutState == shootoutInitWait)
    {

        if (millis_blink_250_750ms())
        {
            setStandardTextToTextHANDLE(RANDOM);
        }
        else
        {
            ledDisp->setNumberToDisplayAsDecimal((int16_t)SHOOTOUT_RANDOM_WAIT_TIME_MAX_SECONDS);
        }
    }
    else
    {
        // the decimal points are a dividor between player's scores.
        ledDisp->setDecimalPointsToDisplay(B00001111);
    }
}

#endif

void Apps::modeCountingLettersAndChars()
{
    // counting mode: numbers and letters.

    NUMBERS_AND_LETTERS_NUMBER_ELSE_LETTER_MODE = !(binaryInputsToggleValue & (1 << BUTTON_INDEXED_SMALL_1));

    if (this->app_init_edge)
    {
        // LETTERS_AND_CHARS_COUNTER = 0;
        COUNTING_LETTERS_AND_CHARS_TIMER.start(-1000);
        // NUMBERS_AND_LETTERS_COUNT_DOWN_ELSE_UP = true;
    }

    if (binaryInputsEdgeUp & (1 << BUTTON_INDEXED_BIG_1))
    {
        LETTERS_AND_CHARS_COUNTER = 0;
    }

    // auto count
    if (binaryInputsEdgeUp & (1 << BUTTON_INDEXED_SMALL_3))
    {
        if (!NUMBERS_AND_LETTERS_NUMBER_ELSE_LETTER_MODE)
        {
            loadBuzzerTrack(SONG_ALPHABET);
        }
    }

    if (binaryInputsToggleValue & (1 << BUTTON_INDEXED_SMALL_3))
    {
        if (binaryInputsEdgeUp & (1 << BUTTON_INDEXED_BIG_3))
        {
            NUMBERS_AND_LETTERS_COUNT_DOWN_ELSE_UP = false;
        }

        if (binaryInputsEdgeUp & (1 << BUTTON_INDEXED_BIG_2))
        {
            NUMBERS_AND_LETTERS_COUNT_DOWN_ELSE_UP = true;
        }

        // auto mode next item
        if (COUNTING_LETTERS_AND_CHARS_TIMER.getCountDownTimerElapsedAndRestart())
        {
            LETTERS_AND_CHARS_COUNTER += 1 - (2 * NUMBERS_AND_LETTERS_COUNT_DOWN_ELSE_UP);
        }

        // set timer speed
        dialOnEdgeChangeInitTimerPercentage(&COUNTING_LETTERS_AND_CHARS_TIMER);
    }
    else
    {
        // show number right away depending on potentio value
        // LETTERS_AND_CHARS_COUNTER = (int16_t)(encoder_dial->getValueLimited(25 + NUMBERS_AND_LETTERS_NUMBER_ELSE_LETTER_MODE * 75, false)); //1024 to 26 letters.
        LETTERS_AND_CHARS_COUNTER += encoder_dial->getDelta();
        modifyValueUpDownWithButtonsBig2And3(&LETTERS_AND_CHARS_COUNTER);
    }

    // only do the characters of the alphabet in lettermode.
    int16_t maxValue = 9999;
    if (!NUMBERS_AND_LETTERS_NUMBER_ELSE_LETTER_MODE)
    {
        maxValue = 25;
    }
    checkBoundaries(&LETTERS_AND_CHARS_COUNTER, 0, maxValue, true);

    if (NUMBERS_AND_LETTERS_NUMBER_ELSE_LETTER_MODE)
    {
        ledDisp->setNumberToDisplay(LETTERS_AND_CHARS_COUNTER, (binaryInputsToggleValue & (1 << BUTTON_INDEXED_SMALL_2)));
    }
    else
    {
        displayLetterAndPositionInAlphabet(textHandle, LETTERS_AND_CHARS_COUNTER);
    }
}

void Apps::modeSoundSong()
{
    if (this->app_init_edge)
    {
        playSongHappyDryer();
        // MODE_SOUND_SONG_INDEX = 0;
    }

    if (binaryInputsToggleValue & (1 << BUTTON_INDEXED_SMALL_3))
    {
        buzzer->changeTranspose(encoder_dial->getDelta());
    }
    else
    {
        buzzerChangeSpeedRatioWithEncoderDial();
    }

    if (isBigButtonPressEdgeUpDetected())
    {
        uint8_t shift = (4 * ((binaryInputsToggleValue & (1 << BUTTON_INDEXED_SMALL_1)) > 0));
        uint8_t shift_eeprom = (8 * ((binaryInputsToggleValue & (1 << BUTTON_INDEXED_SMALL_2)) > 0));
        loadBuzzerTrack(binaryInputsEdgeUpBigButtonIndex + shift + shift_eeprom);
    }

    buzzer->lastPlayedNoteToDisplay(textHandle, decimalDotsHandle);
}

void Apps::modeComposeSong()
{
    bool displayStagedNote = false;
    int16_t step = 0;

    if (this->app_init_edge)
    {
        for (uint8_t i = 0; i < bytes_array_size; i++)
        {
            COMPOSER_SONG[i] = BUZZER_NOTES_BUFFER_SONG_STOPVALUE;
        }
        COMPOSER_SONG_LENGTH = 1;
        COMPOSER_SONG[0] = SOUND_SONG_COMPOSER_DEFAULT_NOTE; // default note
        COMPOSER_STEP_TIMER.setInitTimeMillis(-200);
    }

    if (binaryInputsToggleValue & (1 << BUTTON_INDEXED_SMALL_1))
    {
        // eeprom load / save
#ifdef ENABLE_EEPROM
        bool loaded;
        loaded = saveLoadMenu(COMPOSER_SONG, 4, EEPROM_COMPOSER_SONG_LENGTH, EEPROM_COMPOSER_SONGS_START_ADDRESS);

        if (loaded)
        {
            COMPOSER_STEP = 0;
            // search for the last note in the composed song.
            // assume last note of longest possible song is always BUZZER_NOTES_BUFFER_SONG_STOPVALUE
            for (uint8_t i = bytes_array_size - 2; i > 0; i--)
            {
                COMPOSER_SONG_LENGTH = i + 1;
                if (COMPOSER_SONG[i] != BUZZER_NOTES_BUFFER_SONG_STOPVALUE)
                {
                    break;
                }
            }
        }
#endif
    }
    else
    {
        // not in eeprom mode

        if (binaryInputsToggleValue & (1 << BUTTON_INDEXED_SMALL_2))
        {
            // display song notes indeces + enable insert and delete position

            if (binaryInputsEdgeUp & (1 << BUTTON_INDEXED_BIG_0))
            {
                // delete current position
                if (COMPOSER_SONG_LENGTH <= 0)
                {
                    // empty songs stay empty.
                }
                else
                {
                    // move all notes one position down.
                    for (uint8_t i = COMPOSER_STEP; i < bytes_array_size - 1; i++)
                    {
                        COMPOSER_SONG[i] = COMPOSER_SONG[i + 1];
                    }
                    // deleted space should be a song stop note.
                    COMPOSER_SONG[COMPOSER_SONG_LENGTH - 1] = BUZZER_NOTES_BUFFER_SONG_STOPVALUE;

                    // adjust length
                    COMPOSER_SONG_LENGTH--;
                }
            }

            if (binaryInputsEdgeUp & (1 << BUTTON_INDEXED_BIG_1))
            {
                // insert after current index (and move to it)
                if (COMPOSER_SONG_LENGTH >= bytes_array_size - 2)
                {
                    // max length reached
                }
                else
                {
                    // remember, last note of longest song possible MUST be BUZZER_NOTES_BUFFER_SONG_STOPVALUE, don't copy a note to it.
                    for (uint8_t i = bytes_array_size - 3; i > COMPOSER_STEP; i--)
                    {
                        COMPOSER_SONG[i + 1] = COMPOSER_SONG[i];
                    }
                    COMPOSER_SONG[COMPOSER_STEP + 1] = SOUND_SONG_COMPOSER_DEFAULT_NOTE;
                    COMPOSER_SONG_LENGTH++;
                    step = 1; // move to new position
                }
            }
            ledDisp->setNumberToDisplayAsDecimal(COMPOSER_STEP);
        }
        else
        {
            // display song notes + enable programming and listening to notes

            // select a note
            if ((binaryInputsValue & (1 << BUTTON_INDEXED_BIG_1)))
            {
                displayStagedNote = true;

                bool change = false;
                change = stepChange(&COMPOSER_STAGED_NOTE, encoder_dial->getDelta(), 0, 255, true);
                if (change)
                {
                    buzzerSilentClearBufferAndAddNote((uint8_t)COMPOSER_STAGED_NOTE);
                }

                // let the program button blink to invite it for being pressed.
                // if (millis_half_second_period())
                // {
                //     lights |= 1 << LIGHT_BUTTON_BIG_0;
                // }
                button_light_blink_half_second_period(LIGHT_BUTTON_BIG_0);

                // program note in song when the combination of the two buttons is pressed.
                if (binaryInputsEdgeUp & (1 << BUTTON_INDEXED_BIG_0))
                {
                    COMPOSER_SONG[COMPOSER_STEP] = (uint8_t)COMPOSER_STAGED_NOTE;
                    // buzzerSilentClearBufferAndAddNote(COMPOSER_SONG[COMPOSER_STEP]);

                    // if note added to end, expand song length and add default note
                    if (COMPOSER_STEP == COMPOSER_SONG_LENGTH - 1)
                    {
                        COMPOSER_SONG_LENGTH++;
                        // COMPOSER_SONG[COMPOSER_SONG_LENGTH - 1] = SOUND_SONG_COMPOSER_DEFAULT_NOTE; //default note
                        COMPOSER_SONG[COMPOSER_SONG_LENGTH - 1] = BUZZER_NOTES_BUFFER_SONG_STOPVALUE; // default note
                    }
                }
            }

            // display song notes + enable programming and listening to notes
            if ((binaryInputsEdgeUp & (1 << BUTTON_INDEXED_BIG_1)))
            {
                buzzerSilentClearBufferAndAddNote((uint8_t)COMPOSER_STAGED_NOTE);
            }

            if (binaryInputsEdgeUp & (1 << BUTTON_INDEXED_BIG_0))
            {
                // just listen to note on index in song
                // will also sound when just being programmed
                buzzerSilentClearBufferAndAddNote(COMPOSER_SONG[COMPOSER_STEP]);
            }
        }

        modifyValueUpDownWithButtonsBig2And3(&step);

        // autoplay
        if (binaryInputsToggleValue & (1 << BUTTON_INDEXED_SMALL_3))
        {
            if (COMPOSER_STEP_TIMER.getCountDownTimerElapsedAndRestart())
            {
                step = 1;
            }
        }

        // default potentio behaviour
        // byte big_buttons_mask = 1 << BUTTON_INDEXED_BIG_0 | 1 << BUTTON_INDEXED_BIG_1 | 1 << BUTTON_INDEXED_BIG_2 | 1 << BUTTON_INDEXED_BIG_3;
        // if (isABigButtonPressed() == 0) // no buttons pressed
        if (!isABigButtonPressed()) // no buttons pressed
        {
            if (binaryInputsToggleValue & (1 << BUTTON_INDEXED_SMALL_3))
            {
                // change speed if default behaviour of potentio.
                // COMPOSER_STEP_TIMER.setInitTimeMillis(COMPOSER_STEP_TIMER.getInitTimeMillis() + encoder_dial->getDelta() * 10); //step +1 or -1
                dialOnEdgeChangeInitTimerPercentage(&COMPOSER_STEP_TIMER);
            }
            else
            {
                step = encoder_dial->getDelta(); ////step +1 or -1
            }
        }

        if (step != 0)
        {
            nextStepRotate(&COMPOSER_STEP, (step + 1) / 2, 0, COMPOSER_SONG_LENGTH - 1);
            // stepChange(&COMPOSER_STEP, step, 0, COMPOSER_SONG_LENGTH - 1, true);
            addNoteToBuzzer(COMPOSER_SONG[COMPOSER_STEP]);
        }

        if (binaryInputsToggleValue & (1 << BUTTON_INDEXED_SMALL_2))
        {
            ledDisp->setNumberToDisplayAsDecimal(COMPOSER_STEP);
        }
        else if (displayStagedNote)
        {
            noteToDisplay((uint8_t)COMPOSER_STAGED_NOTE);
        }
        else
        {
            noteToDisplay(COMPOSER_SONG[COMPOSER_STEP]);
        }
    }
}

void Apps::modeSoundNotesInitScale()
{
    SOUND_NOTES_NOTE_INDEX = SOUND_NOTES_SCALE_ROOT;
    SOUND_NOTES_NOTE_ON_SCALE_INDEX = 0;
    SOUND_NOTE_PLAY_NOTE = true;
}

void Apps::modeSoundNotes()
{
    bool update_note = false;
    SOUND_NOTE_MUTE = false;

    if (this->app_init_edge)
    {
        SOUND_NOTES_PROGRESSION_MODE = SOUND_NOTE_MODE_MANUAL;

        // initiateCountDowntimerWith500Millis(&SOUND_NOTE_AUTO_TIMER);
        SOUND_NOTES_SCALE_ROOT = C5_4;
        modeSoundNotesInitScale();

        SOUND_NOTE_SETTING_TEXT_TO_DISPLAY = SOUND_NOTE_DISPLAY_NOTE;
    }

    if (binaryInputsToggleValue & (1 << BUTTON_INDEXED_SMALL_3))
    {
        // auto play
        if (SOUND_NOTE_AUTO_TIMER.getCountDownTimerElapsedAndRestart())
        {
            update_note = true;
        }
        dialOnEdgeChangeInitTimerPercentage(&SOUND_NOTE_AUTO_TIMER);
    }
    else
    {
        int8_t encoder_delta = encoder_dial->getDelta();
        // change note with dial
        if (encoder_delta)
        {
            SOUND_NOTE_AUTO_UP_ELSE_DOWN = encoder_delta > 0;
            update_note = true;
        }
    }

    // advanced vs simple controls
    if (binaryInputsToggleValue & (1 << BUTTON_INDEXED_SMALL_1))
    {
        // advanced

        // change note length
        if (binaryInputsEdgeUp & (1 << BUTTON_INDEXED_BIG_0))
        {
            buzzer->changeNoteToNextLength(&SOUND_NOTES_NOTE_INDEX);
            SOUND_NOTE_PLAY_NOTE = true;
            SOUND_NOTE_SETTING_TEXT_TO_DISPLAY = SOUND_NOTE_DISPLAY_NOTE;
        }

        // change key
        if (binaryInputsEdgeUp & (1 << BUTTON_INDEXED_BIG_1)) // set key when changing scale
        {
            // first keypress, set note to root. (which is done in modeSoundNotesInitScale(); )
            // second keypress, change root.
            if (SOUND_NOTES_NOTE_INDEX == SOUND_NOTES_SCALE_ROOT)
            {
                SOUND_NOTES_SCALE_ROOT++; // transpose to next note on harmonic scale
                if (SOUND_NOTES_SCALE_ROOT > B5_4)
                {
                    SOUND_NOTES_SCALE_ROOT = C5_4;
                }
            }
            modeSoundNotesInitScale();
            SOUND_NOTE_SETTING_TEXT_TO_DISPLAY = SOUND_NOTE_DISPLAY_NOTE;
        }

        //  change scale
        if (binaryInputsEdgeUp & (1 << BUTTON_INDEXED_BIG_2))
        {
            nextStepRotate(&SOUND_NOTES_SCALE_INDEX, 1, 0, SCALES_COUNT);
            modeSoundNotesInitScale();
            SOUND_NOTE_SETTING_TEXT_TO_DISPLAY = 76 + SOUND_NOTES_SCALE_INDEX * 4; // set text offset
        }

        // change progression mode
        if (binaryInputsEdgeUp & (1 << BUTTON_INDEXED_BIG_3))
        {
            SOUND_NOTES_PROGRESSION_MODE++;
            if (SOUND_NOTES_PROGRESSION_MODE > 5)
            {
                SOUND_NOTES_PROGRESSION_MODE = SOUND_NOTE_MODE_MANUAL;
            }
            SOUND_NOTE_SETTING_TEXT_TO_DISPLAY = 96 + 4 * SOUND_NOTES_PROGRESSION_MODE;
        }
    }
    else
    {
        // simple

        SOUND_NOTE_SETTING_TEXT_TO_DISPLAY = SOUND_NOTE_DISPLAY_NOTE;

        // mute button to silently change notes.
        // this allows the box to be used as a primitive piano.
        if (binaryInputsValue & (1 << BUTTON_INDEXED_BIG_0))
        {
            SOUND_NOTE_MUTE = true;
        }

        // just play the active note
        if (binaryInputsEdgeUp & (1 << BUTTON_INDEXED_BIG_1))
        {
            SOUND_NOTE_PLAY_NOTE = true;
        }

        // change note up / downwith button press
        if (binaryInputsEdgeUp & (1 << BUTTON_INDEXED_BIG_2) ||
            (binaryInputsEdgeUp & (1 << BUTTON_INDEXED_BIG_3)))
        {
            SOUND_NOTE_AUTO_UP_ELSE_DOWN = (binaryInputsValue & (1 << BUTTON_INDEXED_BIG_3));
            update_note = true;
        }
    }

    if (update_note)
    {
        uint8_t note_jumps = 1;

        // if (SOUND_NOTES_PROGRESSION_MODE != SOUND_NOTE_MODE_MANUAL){
        // 	SOUND_NOTE_AUTO_UP_ELSE_DOWN = SOUND_NOTES_PROGRESSION_MODE == SOUND_NOTE_MODE_ARPEGGIO_UP;

        // }

        switch (SOUND_NOTES_PROGRESSION_MODE)
        {
        case SOUND_NOTE_MODE_RANDOM:
        {
            note_jumps = random(0, 100);
            break;
        }
        case SOUND_NOTE_MODE_ARPEGGIO_SAWTOOTH:
        {

            if (random(0, 5) == 0)
            {
                SOUND_NOTE_AUTO_UP_ELSE_DOWN = !SOUND_NOTE_AUTO_UP_ELSE_DOWN;
            }
            break;
        }
        case SOUND_NOTE_MODE_ARPEGGIO_UP:
        {

            SOUND_NOTE_AUTO_UP_ELSE_DOWN = true;
            break;
        }
        case SOUND_NOTE_MODE_ARPEGGIO_DOWN:
        {

            SOUND_NOTE_AUTO_UP_ELSE_DOWN = false;
            break;
        }
        case SOUND_NOTE_MODE_RANDOM_ERRATIC:
        {
            // this is the more clear version, but takes 12bytes of memory more:
            // SOUND_NOTE_AUTO_UP_ELSE_DOWN = (bool)random(0, 2);
            // note_jumps = random(0, 3);

            // less memory intensive:
            uint8_t tmp = random(0, 6);
            SOUND_NOTE_AUTO_UP_ELSE_DOWN = tmp > 2;
            note_jumps = tmp / 2;

            break;
        }
        }

        // every jump is one step on the scale.
        for (uint8_t note_jump = 0; note_jump < note_jumps; note_jump++)
        {
            // which scale are we on
            uint8_t scale_start_index = pgm_read_byte_near(scale_start_indeces + SOUND_NOTES_SCALE_INDEX);

            uint8_t distance_to_next_note_on_scale = pgm_read_byte_near(scales + scale_start_index + SOUND_NOTES_NOTE_ON_SCALE_INDEX);

            // next index on scale
            nextStepRotate(&SOUND_NOTES_NOTE_ON_SCALE_INDEX,
                           SOUND_NOTE_AUTO_UP_ELSE_DOWN,
                           0,
                           (int16_t)pgm_read_byte_near(scale_lengths + SOUND_NOTES_SCALE_INDEX));

            if (!SOUND_NOTE_AUTO_UP_ELSE_DOWN)
            {
                distance_to_next_note_on_scale = pgm_read_byte_near(scales + scale_start_index + SOUND_NOTES_NOTE_ON_SCALE_INDEX);
            }

            // take number of steps on the chromatic scale to go to desired note
            for (uint8_t i = 0; i < distance_to_next_note_on_scale; i++)
            {
                // buzzer->nextNote(
                // &SOUND_NOTES_NOTE_INDEX,
                // SOUND_NOTE_AUTO_UP_ELSE_DOWN,
                // true);
                int16_t limit = (SOUND_NOTES_NOTE_INDEX / NOTES_COUNT) * NOTES_COUNT;
                // nextStepRotate(&SOUND_NOTES_NOTE_INDEX,SOUND_NOTE_AUTO_UP_ELSE_DOWN, limit,limit+NOTES_COUNT);

                nextStepRotate(&SOUND_NOTES_NOTE_INDEX, SOUND_NOTE_AUTO_UP_ELSE_DOWN, limit, limit + NOTES_COUNT - 1);

                // //(SOUND_NOTES_NOTE_INDEX % NOTES_COUNT) * NOTES_COUNT, (SOUND_NOTES_NOTE_INDEX % NOTES_COUNT) + 1) * NOTES_COUNT);
            }
        }

        // SOUND_NOTE_SETTING_TEXT_TO_DISPLAY = SOUND_NOTE_DISPLAY_NOTE; // don't add here, when in auto play in advance mode, the settings text should stay visible.
        SOUND_NOTE_PLAY_NOTE = true;
    }

    if (SOUND_NOTE_PLAY_NOTE && !SOUND_NOTE_MUTE)
    {
        if (binaryInputsToggleValue & (1 << BUTTON_INDEXED_SMALL_2))
        {
            buzzerSilentClearBuffer();
        }
        addNoteToBuzzer(SOUND_NOTES_NOTE_INDEX);
    }
    SOUND_NOTE_PLAY_NOTE = false;

    // index to actual note on the scale
    // USE A TIMER to end display of settings. hmmm not sure if it will be that much better...
    if (SOUND_NOTE_SETTING_TEXT_TO_DISPLAY == SOUND_NOTE_DISPLAY_NOTE)
    {
        noteToDisplay(SOUND_NOTES_NOTE_INDEX);
    }
    else
    {
        setStandardTextToTextHANDLE(SOUND_NOTE_SETTING_TEXT_TO_DISPLAY);
    }
}

void Apps::modeMovie()
{
    bool sound_on = false;
    bool reload_soundtrack = false;
    bool movie_restart = false;

    // reset saved led disp state.
    if (this->app_init_edge)
    {
        // MOVIE_MODE_FRAME_INTERVAL_TIMER.start(-500);
        // initiateCountDowntimerWith500Millis(&MOVIE_MODE_FRAME_INTERVAL_TIMER);
        loadNextMovie();
        MOVIE_MODE_RESTART_SOUNDTRACK_AT_MOVIE_START = true;
    }

    // sound ON/OFF

    sound_on = !(binaryInputsToggleValue & (1 << BUTTON_INDEXED_SMALL_2));

    if (binaryInputsToggleValue & (1 << BUTTON_INDEXED_SMALL_1))
    {
        // sound settings
        reload_soundtrack = modifyValueUpDownWithButtonsBig2And3(&MOVIE_MODE_SOUNDTRACK_INDEX);

        if (binaryInputsEdgeUp & (1 << BUTTON_INDEXED_BIG_1))
        {
            MOVIE_MODE_RESTART_SOUNDTRACK_AT_MOVIE_START = !MOVIE_MODE_RESTART_SOUNDTRACK_AT_MOVIE_START;
        }

        if (binaryInputsEdgeUp & (1 << BUTTON_INDEXED_BIG_0))
        {
            reload_soundtrack = true;
        }
    }
    else
    {
        if (binaryInputsToggleValue & (1 << BUTTON_INDEXED_SMALL_3))
        {
            // manual mode
            MOVIE_MODE_FLASH_FRAME_INDEX += encoder_dial->getDelta();

            // step mode
            modifyValueUpDownWithButtonsBig2And3(&MOVIE_MODE_FLASH_FRAME_INDEX);
        }
        else
        {
            // auto mode.

            dialOnEdgeChangeInitTimerPercentage(&MOVIE_MODE_FRAME_INTERVAL_TIMER);

            if (binaryInputsEdgeUp & (1 << BUTTON_INDEXED_BIG_2))
            {
                // this->dataPlayer.setSetIndexDirection(2);
                // MOVIE_MODE_AUTO_BACKWARDS = !MOVIE_MODE_AUTO_BACKWARDS;
                MOVIE_MODE_AUTO_BACKWARDS = true;
            }

            if ((binaryInputsValue & (1 << BUTTON_INDEXED_BIG_3)))
            {
                // this->dataPlayer.update(); // this to pause the movie while holding.
                MOVIE_MODE_AUTO_BACKWARDS = false;
            }
        }

        // next movie
        if (binaryInputsEdgeUp & (1 << BUTTON_INDEXED_BIG_0))
        {
            loadNextMovie();
        }

        if (binaryInputsEdgeUp & (1 << BUTTON_INDEXED_BIG_1))
        {
            MOVIE_MODE_SHOW_NEGATIVE = !MOVIE_MODE_SHOW_NEGATIVE;
        }
    }

    if (!(binaryInputsToggleValue & (1 << BUTTON_INDEXED_SMALL_3)))
    {
        if (MOVIE_MODE_FRAME_INTERVAL_TIMER.getCountDownTimerElapsedAndRestart())
        {
            MOVIE_MODE_FLASH_FRAME_INDEX += (1 - 2 * MOVIE_MODE_AUTO_BACKWARDS);
        }
    }

    // check limits of movie
    if (MOVIE_MODE_FLASH_FRAME_INDEX > MOVIE_MODE_MOVIE_FRAME_INDEX_END)
    {
        MOVIE_MODE_FLASH_FRAME_INDEX = MOVIE_MODE_MOVIE_FRAME_INDEX_START;
        movie_restart = true;
    }
    else if (MOVIE_MODE_FLASH_FRAME_INDEX < (int16_t)MOVIE_MODE_MOVIE_FRAME_INDEX_START)
    {
        MOVIE_MODE_FLASH_FRAME_INDEX = MOVIE_MODE_MOVIE_FRAME_INDEX_END;
        movie_restart = true;
    }

    if (MOVIE_MODE_RESTART_SOUNDTRACK_AT_MOVIE_START)
    {
        reload_soundtrack = reload_soundtrack || movie_restart;
    }
    else if (buzzer->buzzerBufferDonePlaying())
    {
        reload_soundtrack = true;
    }

    // soundtrack
    if (reload_soundtrack && sound_on)
    {
        // buzzerSilentClearBuffer();
        loadBuzzerTrack(MOVIE_MODE_SOUNDTRACK_INDEX);
    }

    // graphics
    loadMovieFrame(MOVIE_MODE_FLASH_FRAME_INDEX);

    // invert all data in picture
    if (MOVIE_MODE_SHOW_NEGATIVE)
    {
        // negative .
        displayAllSegments = ~displayAllSegments;
    }

    // set to display
    displayAllSegmentsToScreen();
}

bool Apps::loadMovieFrame(int16_t frame_index)
{
    this->displayAllSegments = 0;

    if (frame_index < MAX_FRAMES_MOVIES_FLASH)
    {
        // flash
        flashPictureToDisplayAllSegments(disp_4digits_animations + frame_index * 4);
    }
    else
    {
        // eeprom
        eepromPictureToDisplayAllSegments(frame_index - MAX_FRAMES_MOVIES_FLASH);
    }

    // check for end of movie
    uint32_t stop_screen = (uint32_t)ANIMATION_STOP_CODE_PART_0 << 0 | (uint32_t)ANIMATION_STOP_CODE_PART_1 << 8 | (uint32_t)ANIMATION_STOP_CODE_PART_2 << 16 | (uint32_t)ANIMATION_STOP_CODE_PART_3 << 24;

    if (displayAllSegments == stop_screen)
    {
        return false;
    }
    else
    {
        return true;
    }
}

void Apps::loadNextMovie()
{
    bool foundStartOfMovie = false;

    // iterate until a stop frame is found check for stop frame
    while (loadMovieFrame(MOVIE_MODE_FLASH_FRAME_INDEX) || !foundStartOfMovie)
    {
        // check if over limit (last movie)
        if (MOVIE_MODE_FLASH_FRAME_INDEX >= (MAX_FRAMES_MOVIES_FLASH
#ifdef ENABLE_EEPROM
                                             + EEPROM_NUMBER_OF_DRAWINGS
#endif
                                             ))

        {
            foundStartOfMovie = true;
            MOVIE_MODE_MOVIE_FRAME_INDEX_START = 1;
            MOVIE_MODE_FLASH_FRAME_INDEX = 1;
        }

        // set variables presuming that this could be the last iteration of the while loop.
        if (!foundStartOfMovie)
        {
            MOVIE_MODE_MOVIE_FRAME_INDEX_START = MOVIE_MODE_FLASH_FRAME_INDEX + 1;
        }
        else
        {
            MOVIE_MODE_MOVIE_FRAME_INDEX_END = MOVIE_MODE_FLASH_FRAME_INDEX;
        }

        if (!loadMovieFrame(MOVIE_MODE_FLASH_FRAME_INDEX))
        {
            foundStartOfMovie = true;
        }

        MOVIE_MODE_FLASH_FRAME_INDEX++;
    }
}

void Apps::displayChangeGlobal(uint32_t *display_buffer)
{
    // global picture operations

    // WARNING, nonkel Lode took this out this function to save some measly bytes. But, just so you know, if you ever add stuff here, look for DRAW_SHOW_MODE everywhere in the code and change it accordingly.
    // if (saveStateToBuffer)
    // {
    // 	DRAW_SHOW_MODE = 4; // prepare for next button press to save buffer and show inversion.

    // }

    if (binaryInputsEdgeUp & (1 << BUTTON_INDEXED_BIG_1))
    {
        DRAW_SHOW_MODE >= 4 ? DRAW_SHOW_MODE = 0 : DRAW_SHOW_MODE++;

        switch (DRAW_SHOW_MODE)
        {
        case 0:
            // invert
            displayAllSegmentsBuffer = *display_buffer;
            *display_buffer = ~*display_buffer;
            break;

        case 1:
            // blank
            *display_buffer = 0;
            break;

        case 2:
            // special stop frame (for end of animations)
            *display_buffer = (uint32_t)ANIMATION_STOP_CODE_PART_0 << 0 | (uint32_t)ANIMATION_STOP_CODE_PART_1 << 8 | (uint32_t)ANIMATION_STOP_CODE_PART_2 << 16 | (uint32_t)ANIMATION_STOP_CODE_PART_3 << 24;
            break;

        case 3:
            // full
            *display_buffer = 0xFFFFFFFF;
            break;

        case 4:
            // restore
            *display_buffer = displayAllSegmentsBuffer;
        }
    }
}

uint32_t Apps::modeSingleSegmentManipulation(uint32_t *display_buffer)
{
    // return blinking cursor segment.
    // no need to initialize DRAW_CURSOR_INDEX, it get's within boundaries in one cycle. And we don't care about starting position.

    uint8_t segmentMoveIndexed[9] = {0x20, 0x10, 0x00, 0x01, 0x40, 0x08, 0x02, 0x04, 0x80}; // 0x00 for empty . It's good to have spots where the cursor is invisible. In order not to pollute the display if you want to really see your drawing, or want to show it to your mother
    uint32_t cursor_position_on_display;

    // encoder_dial->setSensitivity(2);

    int16_t cursor_position = DRAW_CURSOR_ACTIVE_DIGIT * 9 + DRAW_CURSOR_ACTIVE_SEGMENT_IN_ACTIVE_DIGIT;

    stepChange(&cursor_position, encoder_dial->getDelta(), 0, 35, true);

    DRAW_CURSOR_ACTIVE_DIGIT = cursor_position / 9;
    DRAW_CURSOR_ACTIVE_SEGMENT_IN_ACTIVE_DIGIT = cursor_position % 9;

    if (binaryInputsEdgeUp & (1 << BUTTON_INDEXED_BIG_2))
    {
        // move segment inside digit
        nextStepRotate(&DRAW_CURSOR_ACTIVE_SEGMENT_IN_ACTIVE_DIGIT, true, 0, 8);
    }

    if (binaryInputsEdgeUp & (1 << BUTTON_INDEXED_BIG_3))
    {
        // move digit
        nextStepRotate(&DRAW_CURSOR_ACTIVE_DIGIT, true, 0, 3);
    }

    cursor_position_on_display = (uint32_t)(segmentMoveIndexed[DRAW_CURSOR_ACTIVE_SEGMENT_IN_ACTIVE_DIGIT]) << (DRAW_CURSOR_ACTIVE_DIGIT) * 8;

    // check for global display change
    this->displayChangeGlobal(&displayAllSegments);

    // toggle individual segment
    if (binaryInputsEdgeUp & (1 << BUTTON_INDEXED_BIG_0))
    {
        // drawing or erasing the segment by xor'ing it with the drawing
        *display_buffer ^= cursor_position_on_display;
        DRAW_SHOW_MODE = 4; // prepare for next button press to save buffer and show inversion at next global change button press.
    }

    if (millis_quarter_second_period())
    {
        return cursor_position_on_display;
    }
    else
    {
        return 0;
    }
}
#ifdef ENABLE_DRAW_GAME
void Apps::drawGame()
{
    // shows a picture. After it disappears, you have to draw it exactly as it was.

    uint32_t cursorBlinker = 0;

    if (this->app_init_edge)
    {
        drawGameState = drawGameWaitForStart;
    }

#ifndef ENABLE_SELECT_APPS_WITH_SELECTOR
    lights &= ~(1 << LIGHT_BUTTON_SMALL_3); // set light for sure off
    if (millis_half_second_period())
    {
        lights |= 1 << LIGHT_BUTTON_SMALL_3;
    }
#endif

    switch (drawGameState)
    {
    case drawGameWaitForStart:
    {
        drawGameState = drawGameShowPicture;

        DRAW_GAME_PICTURE_TYPE =
            (((uint8_t)((binaryInputsToggleValue & (1 << BUTTON_INDEXED_SMALL_1)) > 0)) << 1) + ((binaryInputsToggleValue & (1 << BUTTON_INDEXED_SMALL_2)) > 0);

        if (DRAW_GAME_PICTURE_TYPE == DRAW_GAME_CLOCK)
        {
            // learn how to read the clock

            ledDisp->minutesToMinutesHoursString(textBuf, (uint16_t)random(0, 1440));
            textBufToDisplayAllSegments();

            // add hour:minute divider.
            displayAllSegments |= 1UL << 15;
        }
        else if (DRAW_GAME_PICTURE_TYPE == DRAW_GAME_NUMBER)
        {
            // random number
            long r = random(0, 10000);
            numberToBufAsDecimal((int16_t)r);
            textBufToDisplayAllSegments();
        }

        else if (DRAW_GAME_PICTURE_TYPE == DRAW_GAME_WORD)
        {
            // random text
            for (uint8_t i = 0; i < 4; i++)
            {
                long r = random(0, 25);
                textBuf[i] = (char)r + 65;
            }
            textBufToDisplayAllSegments();
        }
        else
        {
            // random segments
            displayAllSegments = 0UL;
            for (uint8_t i = 0; i < 32; i++)
            {
                displayAllSegments |= random(0, 2) << i;
            }
        }
        break;
    }

    case drawGameShowPicture:
    {
        // start game button blinking

        if (binaryInputsEdgeUp & (1 << BUTTON_INDEXED_SMALL_3))
        {
            drawGameState = drawGameDraw;
            displayAllSegmentsBuffer = displayAllSegments;
            displayAllSegments = 0;
        }
        byte small_buttons_mask = 1 << BUTTON_INDEXED_SMALL_1 | 1 << BUTTON_INDEXED_SMALL_2;
#ifdef ENABLE_SELECT_APPS_WITH_SELECTOR
        if (millis_half_second_period())
        {
            lights |= 1 << LIGHT_BUTTON_SMALL_3;
        }
        if (((binaryInputsEdgeDown | binaryInputsEdgeUp) & small_buttons_mask) != 0) // a button edge detected
#else
            if (((binaryInputsEdgeUp)&small_buttons_mask) != 0) // a button edge detected
#endif
        {
            drawGameState = drawGameWaitForStart;
        }
        break;
    }

    case drawGameDraw:
    {
        cursorBlinker = modeSingleSegmentManipulation(&displayAllSegments);
        // bug: you can't use this because of same buffer reuse. displayChangeGlobal(&displayAllSegments, false);
#ifdef ENABLE_SELECT_APPS_WITH_SELECTOR
        if ((binaryInputsEdgeUp | binaryInputsEdgeDown) & (1 << BUTTON_INDEXED_SMALL_3))
#else
            if ((binaryInputsEdgeUp) & (1 << BUTTON_INDEXED_SMALL_3))
#endif
        {
            drawGameState = drawGameEvaluate;
            DRAW_GAME_DISPLAY_TIMER.start();

            if (displayAllSegments == displayAllSegmentsBuffer)
            {
                playSongHappyDryer();
            }
            else
            {
                loadBuzzerTrack(SONG_DRYER_UNHAPPY);
            }
        }
        break;
    }

    case drawGameEvaluate:
    {
#ifdef ENABLE_SELECT_APPS_WITH_SELECTOR
        // wait for user input to continue.
        // byte big_buttons_mask = 1 << BUTTON_INDEXED_BIG_0 | 1 << BUTTON_INDEXED_BIG_1 | 1 << BUTTON_INDEXED_BIG_2 | 1 << BUTTON_INDEXED_BIG_3;
        if ((binaryInputsEdgeUp & BIG_BUTTON_MASK) != 0) // a button pressed
        {
            drawGameState = drawGameWaitForStart;
        }
        if (millis_half_second_period())
        {
            lights |= 1 << LIGHT_BUTTON_BIG_0;
        }
#else
            if ((binaryInputsEdgeUp) & (1 << BUTTON_INDEXED_SMALL_3))
            {
                drawGameState = drawGameWaitForStart;
            }

#endif

        // show difference result with original drawing
        if (DRAW_GAME_DISPLAY_TIMER.getEdgeSinceLastCallFirstGivenHundredsPartOfSecond(500, true, true))
        {
            uint32_t displayAllSegments_swap_buffer;
            displayAllSegments_swap_buffer = displayAllSegments;
            displayAllSegments = displayAllSegmentsBuffer;
            displayAllSegmentsBuffer = displayAllSegments_swap_buffer;
        }
        break;
    }

    default:
        break;
    }

    setButtonLight(LIGHT_BUTTON_SMALL_1, DRAW_GAME_PICTURE_TYPE / 2);
    setButtonLight(LIGHT_BUTTON_SMALL_2, DRAW_GAME_PICTURE_TYPE % 2);

    ledDisp->setBinaryToDisplay(displayAllSegments ^ cursorBlinker);
}
#endif // ENABLE_DRAW_GAME
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
