hyperlode/luciebox/Luciebox/ButtonsDacR2r.cpp

#include "ButtonsDacR2r.h"
#include "Arduino.h"

//R-2R ladder --> DAC.  make sure the buttons have Normal Open and Normal Closed positions. Because, they should provide GND at OFF and VCC at ON.

//empty constructor
ButtonsDacR2r::ButtonsDacR2r()
{
    this->debounceMillis = DEBOUNCE_BUTTON_MILLIS;
}

void ButtonsDacR2r::setDebounceMillis(uint8_t value)
{
    this->debounceMillis = (unsigned long)value;
}

void ButtonsDacR2r::setPin(byte pin, byte buttonsCount, uint16_t *thresholds)
{
    this->analogPin = pin;
    this->buttonsCount = buttonsCount;
    this->thresholds = thresholds;
}

uint8_t ButtonsDacR2r::getButtonsValueRaw()
{
    int16_t raw = (int16_t)(analogRead(this->analogPin));
    uint8_t allButtonsState = 0b00000000; //every bit is a button.
    for (uint8_t i = 0; i < this->buttonsCount; i++)
    {
        int16_t checkValue = (int16_t)this->thresholds[i];
        //Serial.println(checkValue -(VALUE_MARGIN_FOR_SELECTOR/2));
        //Serial.println(i);
        //Serial.println("====");

        // value margin is always the binary value one level below the lowest button value
        /*
    value margin example:
    00000000001 //start
    10000000000 //1024 = 2^10
    01000000000 // /2 because 512 would be the next lowest value
    00000010000 //  /2 because we take only half of the margin to end up in the middle
    */
        int16_t value_margin = (int16_t)0b00000001 << (ADC_POWERS_OF_TWO - this->buttonsCount - 2); //((ADC_POWERS_OF_TWO) - this->buttonsCount - 1(for going one level below least buttonvalue) - 1(for dividing into two, so we end up in the middle of the margin) ;

        if (raw > (checkValue - value_margin))
        {
            //Serial.println(raw);
            //Serial.println(checkValue);
            //Serial.println((raw -(VALUE_MARGIN_FOR_SELECTOR/2)));

            allButtonsState |= 0b00000001 << (this->buttonsCount - 1 - i);

            raw -= checkValue;
            if (raw < 0)
            {
                raw = 0;
            }
        }
    }

    return allButtonsState;
}

bool ButtonsDacR2r::getButtonValueByIndex(uint8_t index)
{
    return (0b00000001 << index) & (this->getButtonsValue());
}

uint8_t ButtonsDacR2r::getButtonsValue()
{
    //returns the STABLE value
    return this->buttonsCurrentStableValue;
}

bool ButtonsDacR2r::getValueChangedEdge()
{
    //will only trigger if a change in STABLE value is detected.
    return this->buttonsPreviousStableValue != this->buttonsCurrentStableValue;
}

void ButtonsDacR2r::refresh()
{
    //call this to update the value of the analog input. call multiple times to check for stable value.
    this->buttonsPreviousStableValue = this->buttonsCurrentStableValue;
    uint8_t buttonsValue = getButtonsValueRaw();

    // software debouncing: wait some time to make sure value is stable.
    // reset wait time when value changes.

    if (buttonsValue != this->buttonsPreviousValue)
    {
        this->buttonEdgeMillis = millis();
        this->debounceMillis = DEBOUNCE_BUTTON_MILLIS;
    }

    if (millis() - this->buttonEdgeMillis > this->debounceMillis)
    {
        this->debounceMillis = 1000000;
        this->buttonsCurrentStableValue = buttonsValue;
    }

    this->buttonsPreviousValue = buttonsValue;
}
